techav-homebrew/Wrap030-ATX/Mainboard/Bus-Ctrl.kicad_sch

## KiCad design Mainboard/Bus-Ctrl.kicad_sch (2023-04-03)

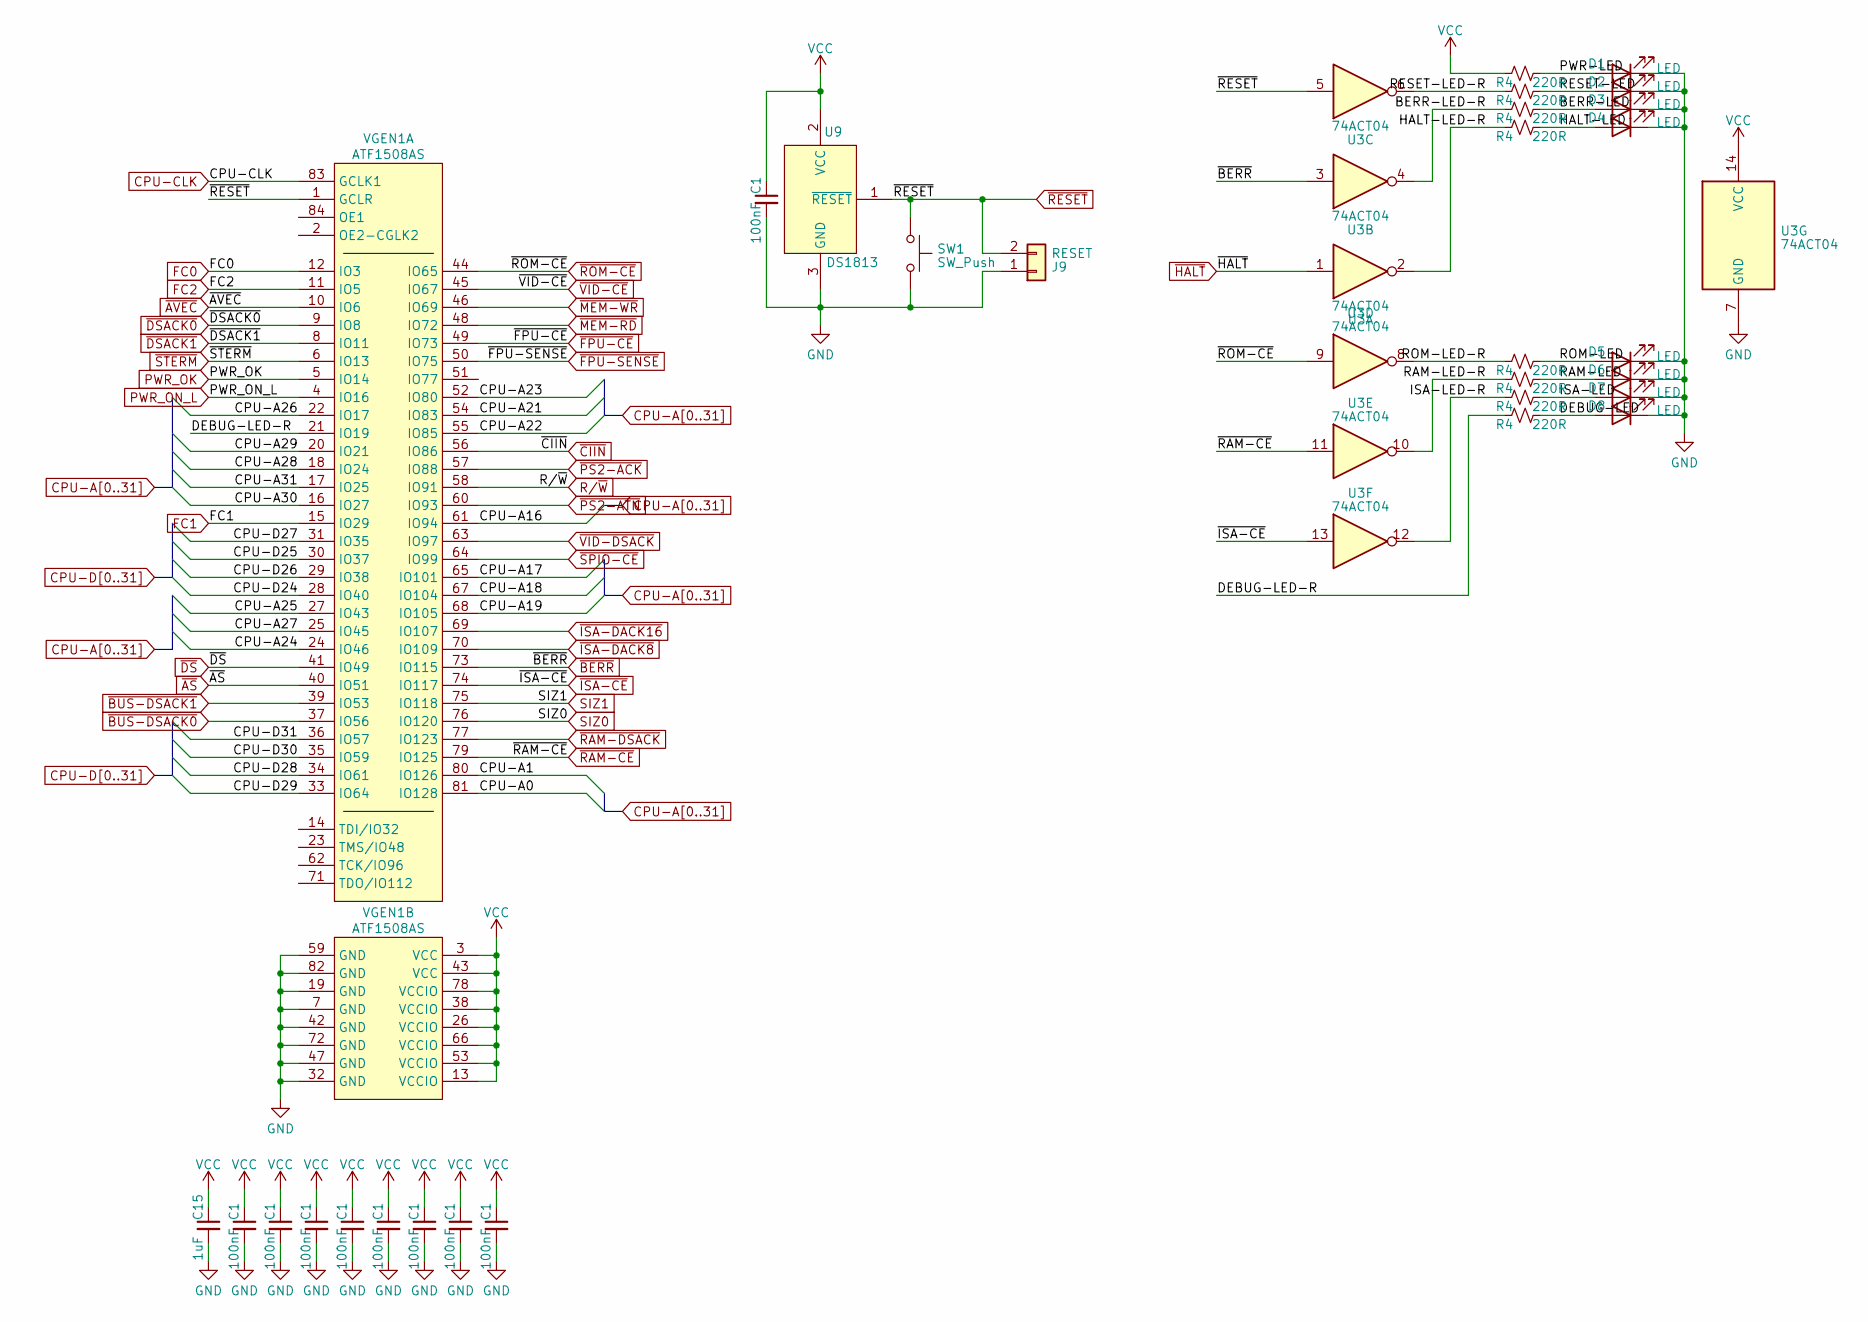
[picture p3: schematic Bus-Ctrl.kicad_sch]

Parts:
C1: 100nF; C_0402_1005Metric_Pad0.74x0.62mm_HandSolder; Mouser-Part 187-CL05B104KO5NNNC
C15: 1uF; C_0402_1005Metric_Pad0.74x0.62mm_HandSolder; Mouser-Part 187-CL05A105KA5NQNC
D1, D2, D3, D4, D5, D6, D7, D8: LED; LED_D3.0mm; Mouser-Part 859-LTL1CHJETNN
J9: RESET; PinHeader_1x02_P2.54mm_Vertical; Mouser-Part 523-G800NA306018EU
R4: 220R; R_0402_1005Metric_Pad0.72x0.64mm_HandSolder; Mouser-Part 303-0402WGF2200TCE
SW1: SW_Push; SW_PUSH_6mm; Mouser-Part 179-TS026660BK260LCR
U3: 74ACT04; DIP-14_W7.62mm_Socket; Mouser-Part 595-SN74ACT04N
U9: DS1813; TO-92_Inline; Mouser-Part 700-DS1813-5T&R
VGEN1: ATF1508AS; PLCC-84_THT-Socket; Mouser-Part 556-ATF1508AS-10JU84

Connections:
BERR-LED: D3.2 (A), R4.2
BERR-LED-R: R4.1, U3.4
CPU-A0: VGEN1.81 (IO128)
CPU-A1: VGEN1.80 (IO126)
CPU-A16: VGEN1.61 (IO94)
CPU-A17: VGEN1.65 (IO101)
CPU-A18: VGEN1.67 (IO104)
CPU-A19: VGEN1.68 (IO105)
CPU-A21: VGEN1.54 (IO83)
CPU-A22: VGEN1.55 (IO85)
CPU-A23: VGEN1.52 (IO80)
CPU-A24: VGEN1.24 (IO46)
CPU-A25: VGEN1.27 (IO43)
CPU-A26: VGEN1.22 (IO17)
CPU-A27: VGEN1.25 (IO45)
CPU-A28: VGEN1.18 (IO24)
CPU-A29: VGEN1.20 (IO21)
CPU-A30: VGEN1.16 (IO27)
CPU-A31: VGEN1.17 (IO25)
CPU-CLK: VGEN1.83 (GCLK1)
CPU-D24: VGEN1.28 (IO40)
CPU-D25: VGEN1.30 (IO37)
CPU-D26: VGEN1.29 (IO38)
CPU-D27: VGEN1.31 (IO35)
CPU-D28: VGEN1.34 (IO61)
CPU-D29: VGEN1.33 (IO64)
CPU-D30: VGEN1.35 (IO59)
CPU-D31: VGEN1.36 (IO57)
DEBUG-LED: D8.2 (A), R4.2
DEBUG-LED-R: R4.1, VGEN1.21 (IO19)
FC0: VGEN1.12 (IO3)
FC1: VGEN1.15 (IO29)
FC2: VGEN1.11 (IO5)
GND: C1.2, C15.2, D1.1 (K), D2.1 (K), D3.1 (K), D4.1 (K), D5.1 (K), D6.1 (K), D7.1 (K), D8.1 (K), J9.1, SW1.2, U3.7 (GND), U9.3 (GND), VGEN1.7 (GND), VGEN1.19 (GND), VGEN1.32 (GND), VGEN1.42 (GND), VGEN1.47 (GND), VGEN1.59 (GND), VGEN1.72 (GND), VGEN1.82 (GND)
HALT-LED: D4.2 (A), R4.2
HALT-LED-R: R4.1, U3.2
ISA-LED: D7.2 (A), R4.2
ISA-LED-R: R4.1, U3.12
PWR-LED: D1.2 (A), R4.2
PWR_OK: VGEN1.5 (IO14)
PWR_ON_L: VGEN1.4 (IO16)
RAM-LED: D6.2 (A), R4.2
RAM-LED-R: R4.1, U3.10
RESET-LED: D2.2 (A), R4.2
RESET-LED-R: R4.1, U3.6
ROM-LED: D5.2 (A), R4.2
ROM-LED-R: R4.1, U3.8
R/~W: VGEN1.58 (IO91)
SIZ0: VGEN1.76 (IO120)
SIZ1: VGEN1.75 (IO118)
VCC: C1.1, C15.1, R4.1, U3.14 (VCC), U9.2 (VCC), VGEN1.3 (VCC), VGEN1.13 (VCCIO), VGEN1.26 (VCCIO), VGEN1.38 (VCCIO), VGEN1.43 (VCC), VGEN1.53 (VCCIO), VGEN1.66 (VCCIO), VGEN1.78 (VCCIO)
~AS: VGEN1.40 (IO51)
~AVEC: VGEN1.10 (IO6)
~BERR: U3.3, VGEN1.73 (IO115)
~BUS-DSACK0: VGEN1.37 (IO56)
~BUS-DSACK1: VGEN1.39 (IO53)
~CIIN: VGEN1.56 (IO86)
~DSACK0: VGEN1.9 (IO8)
~DSACK1: VGEN1.8 (IO11)
~DS: VGEN1.41 (IO49)
~FPU-CE: VGEN1.49 (IO73)
~FPU-SENSE: VGEN1.50 (IO75)
~HALT: U3.1
~ISA-CE: U3.13, VGEN1.74 (IO117)
~ISA-DACK8: VGEN1.70 (IO109)
~ISA-DACK16: VGEN1.69 (IO107)
~MEM-RD: VGEN1.48 (IO72)
~MEM-WR: VGEN1.46 (IO69)
~PS2-ACK: VGEN1.57 (IO88)
~PS2-ATN: VGEN1.60 (IO93)
~RAM-CE: U3.11, VGEN1.79 (IO125)
~RAM-DSACK: VGEN1.77 (IO123)
~RESET: J9.2, SW1.1, U3.5, U9.1 (~RESET), VGEN1.1 (GCLR)
~ROM-CE: U3.9, VGEN1.44 (IO65)
~SPIO-CE: VGEN1.64 (IO99)
~STERM: VGEN1.6 (IO13)
~VID-CE: VGEN1.45 (IO67)
~VID-DSACK: VGEN1.63 (IO97)
