techav-homebrew/Wrap030-ATX/Mainboard/IRQ.kicad_sch

## KiCad design Mainboard/IRQ.kicad_sch (2023-04-03)

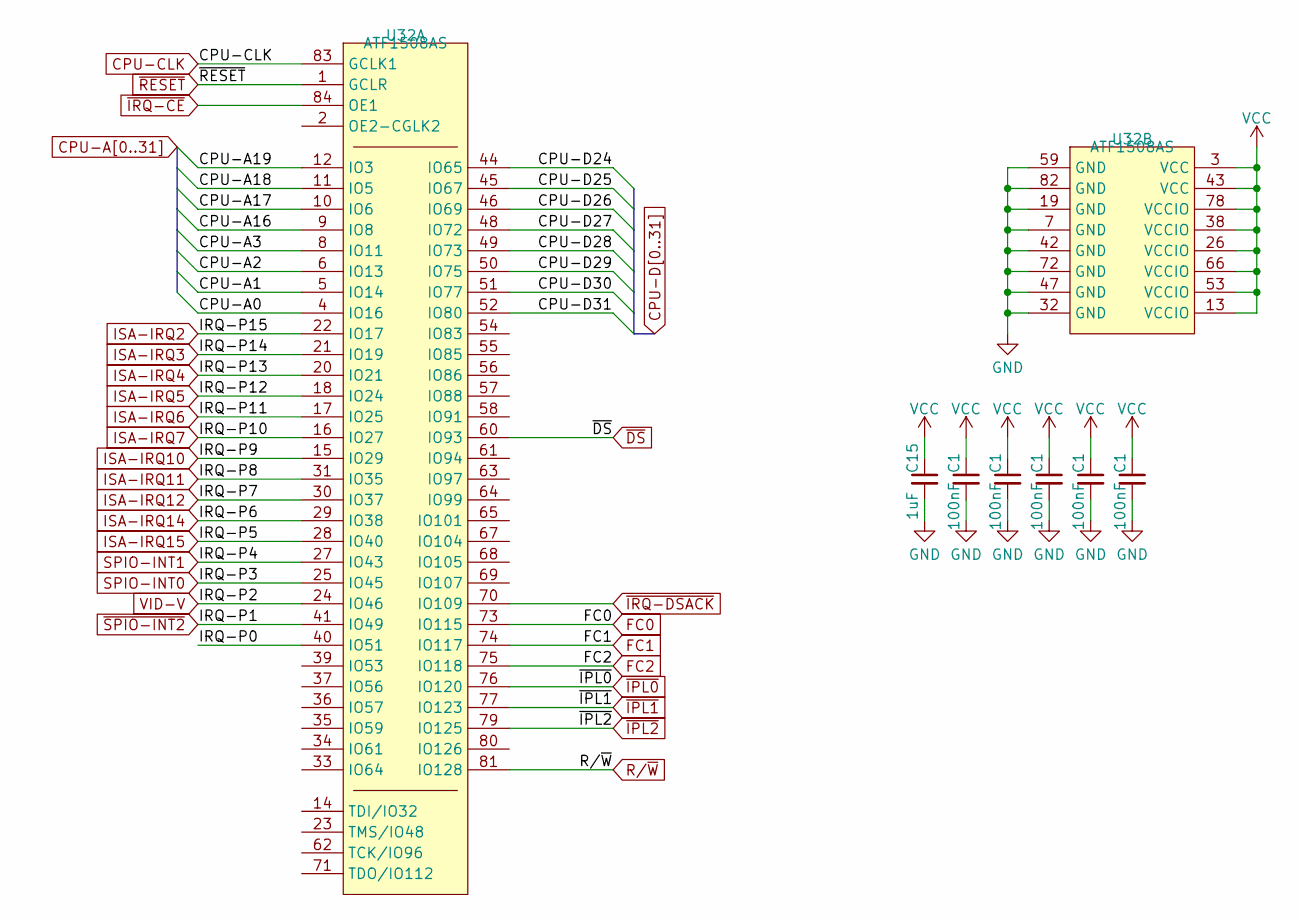
[picture p4: schematic IRQ.kicad_sch]

Parts:
C1: 100nF; C_0402_1005Metric_Pad0.74x0.62mm_HandSolder; Mouser-Part 187-CL05B104KO5NNNC
C15: 1uF; C_0402_1005Metric_Pad0.74x0.62mm_HandSolder; Mouser-Part 187-CL05A105KA5NQNC
U32: ATF1508AS; PLCC-84_THT-Socket; Mouser-Part 556-ATF1508AS-10JU84

Connections:
CPU-A0: U32.4 (IO16)
CPU-A1: U32.5 (IO14)
CPU-A2: U32.6 (IO13)
CPU-A3: U32.8 (IO11)
CPU-A16: U32.9 (IO8)
CPU-A17: U32.10 (IO6)
CPU-A18: U32.11 (IO5)
CPU-A19: U32.12 (IO3)
CPU-CLK: U32.83 (GCLK1)
CPU-D24: U32.44 (IO65)
CPU-D25: U32.45 (IO67)
CPU-D26: U32.46 (IO69)
CPU-D27: U32.48 (IO72)
CPU-D28: U32.49 (IO73)
CPU-D29: U32.50 (IO75)
CPU-D30: U32.51 (IO77)
CPU-D31: U32.52 (IO80)
FC0: U32.73 (IO115)
FC1: U32.74 (IO117)
FC2: U32.75 (IO118)
GND: C1.2, C15.2, U32.7 (GND), U32.19 (GND), U32.32 (GND), U32.42 (GND), U32.47 (GND), U32.59 (GND), U32.72 (GND), U32.82 (GND)
IRQ-P0: U32.40 (IO51)
ISA-IRQ2: U32.22 (IO17)
ISA-IRQ3: U32.21 (IO19)
ISA-IRQ4: U32.20 (IO21)
ISA-IRQ5: U32.18 (IO24)
ISA-IRQ6: U32.17 (IO25)
ISA-IRQ7: U32.16 (IO27)
ISA-IRQ10: U32.15 (IO29)
ISA-IRQ11: U32.31 (IO35)
ISA-IRQ12: U32.30 (IO37)
ISA-IRQ14: U32.29 (IO38)
ISA-IRQ15: U32.28 (IO40)
R/~W: U32.81 (IO128)
SPIO-INT0: U32.25 (IO45)
SPIO-INT1: U32.27 (IO43)
VCC: C1.1, C15.1, U32.3 (VCC), U32.13 (VCCIO), U32.26 (VCCIO), U32.38 (VCCIO), U32.43 (VCC), U32.53 (VCCIO), U32.66 (VCCIO), U32.78 (VCCIO)
VID-V: U32.24 (IO46)
~DS: U32.60 (IO93)
~IPL0: U32.76 (IO120)
~IPL1: U32.77 (IO123)
~IPL2: U32.79 (IO125)
~IRQ-CE: U32.84 (OE1)
~IRQ-DSACK: U32.70 (IO109)
~RESET: U32.1 (GCLR)
~SPIO-INT2: U32.41 (IO49)
