techav-homebrew/Wrap030-ATX/Mainboard/ISA-IDE-Con.kicad_sch

## KiCad design Mainboard/ISA-IDE-Con.kicad_sch (2023-04-03)

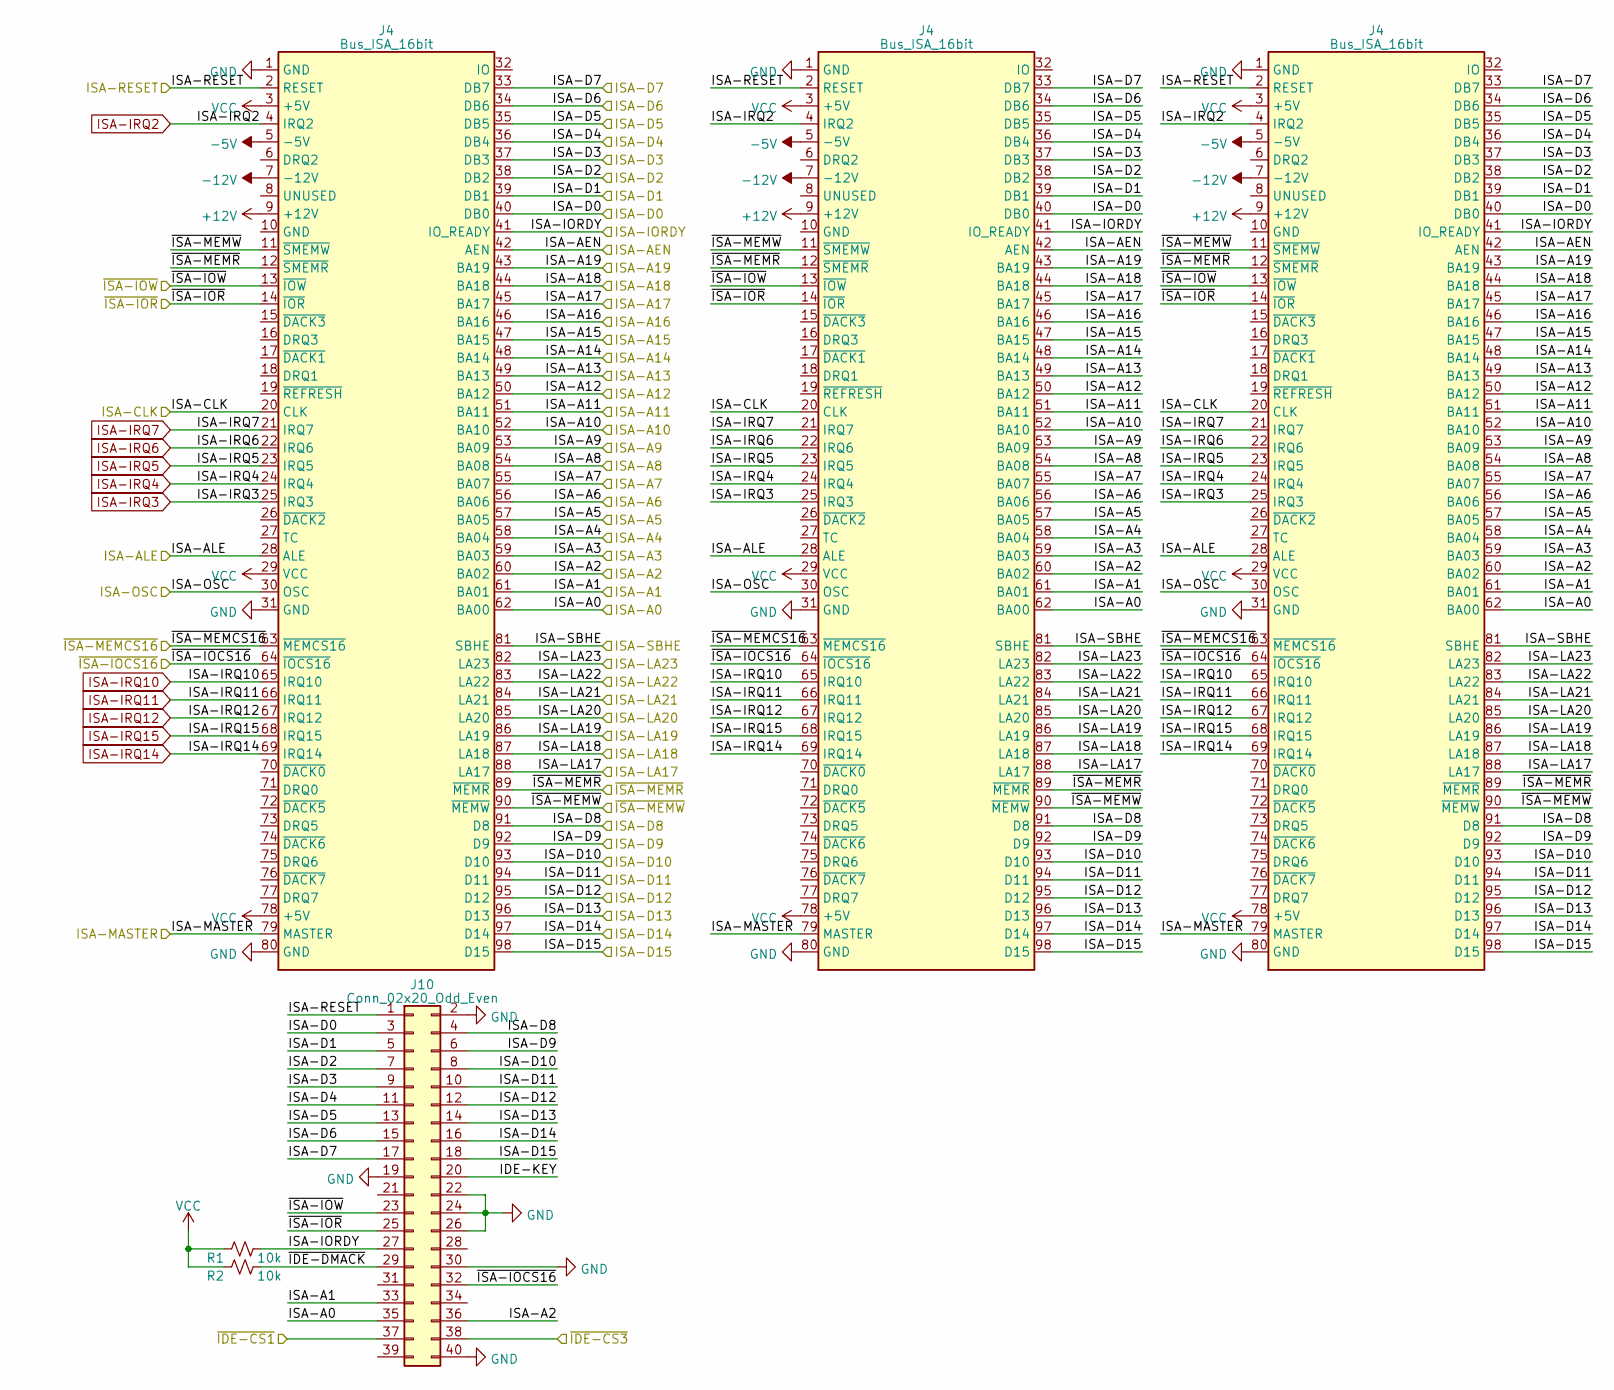
[picture p5: schematic ISA-IDE-Con.kicad_sch]

Parts:
J4: Bus_ISA_16bit; ISA16; Mouser-Part 571-5645169-4
J10: Conn_02x20_Odd_Even; PinHeader_2x20_P2.54mm_Vertical; Mouser-Part 710-61203921621
R1, R2: 10k; R_0402_1005Metric_Pad0.72x0.64mm_HandSolder; Mouser-Part 303-0402WGF1002TCE

Connections:
+12V: J4.9 (+12V)
-5V: J4.5 (-5V)
-12V: J4.7 (-12V)
GND: J4.1 (GND), J4.31 (GND), J4.80 (GND), J10.2, J10.19, J10.22, J10.24, J10.26, J10.30, J10.40
IDE-KEY: J10.20
ISA-A0: J4.62 (BA00), J10.35
ISA-A1: J4.61 (BA01), J10.33
ISA-A2: J4.60 (BA02), J10.36
ISA-A3: J4.59 (BA03)
ISA-A4: J4.58 (BA04)
ISA-A5: J4.57 (BA05)
ISA-A6: J4.56 (BA06)
ISA-A7: J4.55 (BA07)
ISA-A8: J4.54 (BA08)
ISA-A9: J4.53 (BA09)
ISA-A10: J4.52 (BA10)
ISA-A11: J4.51 (BA11)
ISA-A12: J4.50 (BA12)
ISA-A13: J4.49 (BA13)
ISA-A14: J4.48 (BA14)
ISA-A15: J4.47 (BA15)
ISA-A16: J4.46 (BA16)
ISA-A17: J4.45 (BA17)
ISA-A18: J4.44 (BA18)
ISA-A19: J4.43 (BA19)
ISA-AEN: J4.42 (AEN)
ISA-ALE: J4.28 (ALE)
ISA-CLK: J4.20 (CLK)
ISA-D0: J4.40 (DB0), J10.3
ISA-D1: J4.39 (DB1), J10.5
ISA-D2: J4.38 (DB2), J10.7
ISA-D3: J4.37 (DB3), J10.9
ISA-D4: J4.36 (DB4), J10.11
ISA-D5: J4.35 (DB5), J10.13
ISA-D6: J4.34 (DB6), J10.15
ISA-D7: J4.33 (DB7), J10.17
ISA-D8: J4.91 (D8), J10.4
ISA-D9: J4.92 (D9), J10.6
ISA-D10: J4.93 (D10), J10.8
ISA-D11: J4.94 (D11), J10.10
ISA-D12: J4.95 (D12), J10.12
ISA-D13: J4.96 (D13), J10.14
ISA-D14: J4.97 (D14), J10.16
ISA-D15: J4.98 (D15), J10.18
ISA-IORDY: J4.41 (IO_READY), J10.27, R1.2
ISA-IRQ2: J4.4 (IRQ2)
ISA-IRQ3: J4.25 (IRQ3)
ISA-IRQ4: J4.24 (IRQ4)
ISA-IRQ5: J4.23 (IRQ5)
ISA-IRQ6: J4.22 (IRQ6)
ISA-IRQ7: J4.21 (IRQ7)
ISA-IRQ10: J4.65 (IRQ10)
ISA-IRQ11: J4.66 (IRQ11)
ISA-IRQ12: J4.67 (IRQ12)
ISA-IRQ14: J4.69 (IRQ14)
ISA-IRQ15: J4.68 (IRQ15)
ISA-LA17: J4.88 (LA17)
ISA-LA18: J4.87 (LA18)
ISA-LA19: J4.86 (LA19)
ISA-LA20: J4.85 (LA20)
ISA-LA21: J4.84 (LA21)
ISA-LA22: J4.83 (LA22)
ISA-LA23: J4.82 (LA23)
ISA-MASTER: J4.79 (MASTER)
ISA-OSC: J4.30 (OSC)
ISA-RESET: J4.2 (RESET), J10.1
ISA-SBHE: J4.81 (SBHE)
VCC: J4.3 (+5V), J4.29 (VCC), J4.78 (+5V), R1.1, R2.1
~IDE-CS1: J10.37
~IDE-CS3: J10.38
~IDE-DMACK: J10.29, R2.2
~ISA-IOCS16: J4.64 (~IOCS16), J10.32
~ISA-IOR: J4.14 (~IOR), J10.25
~ISA-IOW: J4.13 (~IOW), J10.23
~ISA-MEMCS16: J4.63 (~MEMCS16)
~ISA-MEMR: J4.12 (~SMEMR), J4.89 (~MEMR)
~ISA-MEMW: J4.11 (~SMEMW), J4.90 (~MEMW)
