techav-homebrew/Wrap030-ATX/Mainboard/ISA-IDE.kicad_sch

## KiCad design Mainboard/ISA-IDE.kicad_sch (2023-04-03)

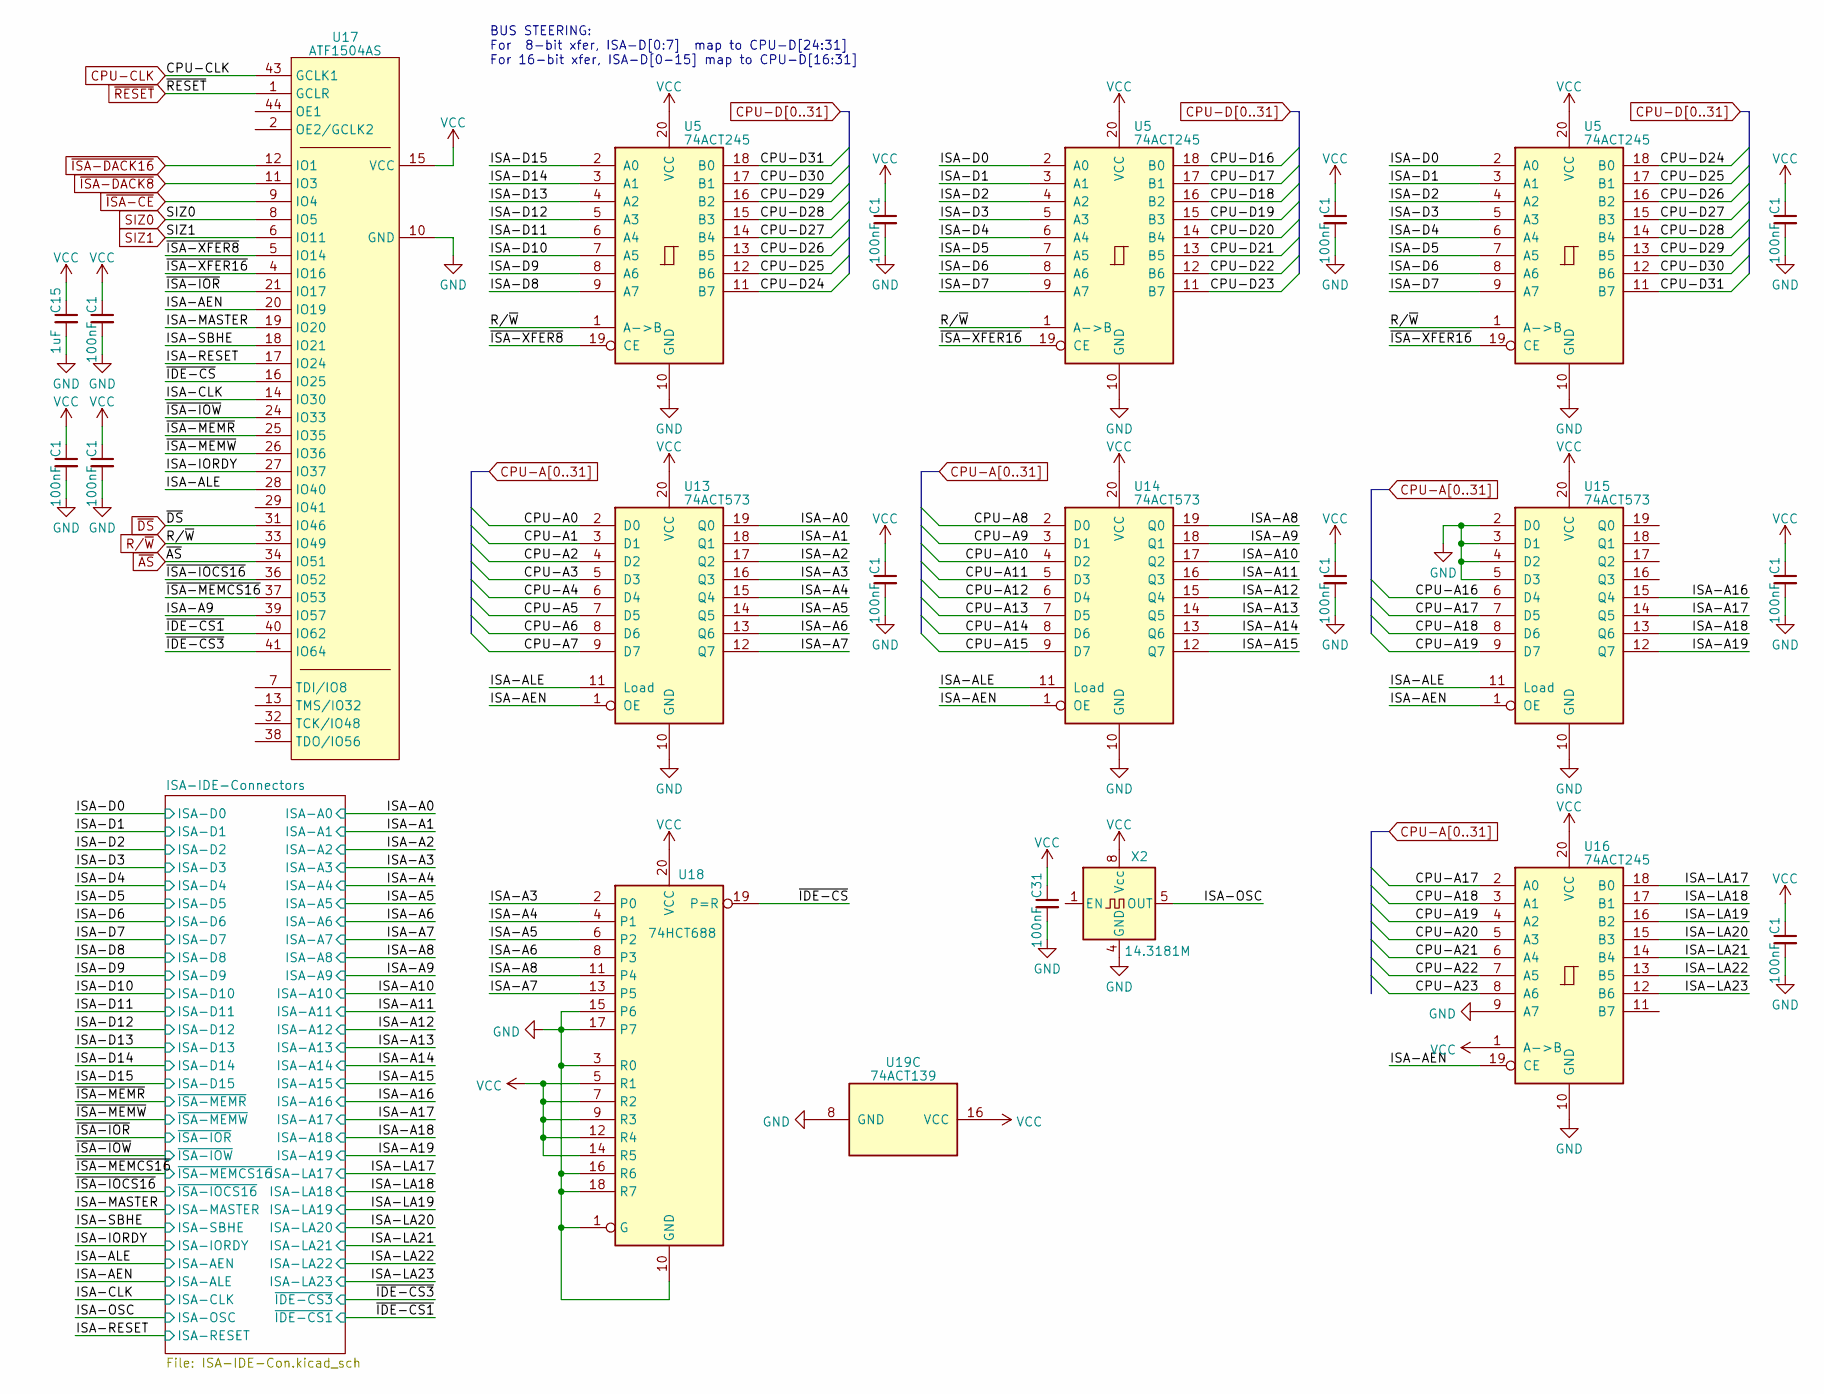
[picture p6: schematic ISA-IDE.kicad_sch]

Parts:
C1, C31: 100nF; C_0402_1005Metric_Pad0.74x0.62mm_HandSolder; Mouser-Part 187-CL05B104KO5NNNC
C15: 1uF; C_0402_1005Metric_Pad0.74x0.62mm_HandSolder; Mouser-Part 187-CL05A105KA5NQNC
U5, U16: 74ACT245; DIP-20_W7.62mm_Socket; Mouser-Part 595-SN74ACT245N
U13, U14, U15: 74ACT573; DIP-20_W7.62mm_Socket; Mouser-Part 595-SN74ACT573N
U17: ATF1504AS; PLCC-44_THT-Socket; Mouser-Part 556-AF1500A10JU
U18: 74HCT688; DIP-20_W7.62mm_Socket; Mouser-Part 595-CD74HCT688EE4
U19: 74ACT139; DIP-16_W7.62mm_Socket; Mouser-Part 595-CD74ACT139E
X2: 14.3181M; Oscillator_DIP-8; Mouser-Part ECS-2100AX-14.31818MHZ

Connections:
CPU-A0: U13.2 (D0)
CPU-A1: U13.3 (D1)
CPU-A2: U13.4 (D2)
CPU-A3: U13.5 (D3)
CPU-A4: U13.6 (D4)
CPU-A5: U13.7 (D5)
CPU-A6: U13.8 (D6)
CPU-A7: U13.9 (D7)
CPU-A8: U14.2 (D0)
CPU-A9: U14.3 (D1)
CPU-A10: U14.4 (D2)
CPU-A11: U14.5 (D3)
CPU-A12: U14.6 (D4)
CPU-A13: U14.7 (D5)
CPU-A14: U14.8 (D6)
CPU-A15: U14.9 (D7)
CPU-A16: U15.6 (D4)
CPU-A17: U15.7 (D5), U16.2 (A0)
CPU-A18: U15.8 (D6), U16.3 (A1)
CPU-A19: U15.9 (D7), U16.4 (A2)
CPU-A20: U16.5 (A3)
CPU-A21: U16.6 (A4)
CPU-A22: U16.7 (A5)
CPU-A23: U16.8 (A6)
CPU-CLK: U17.43 (GCLK1)
CPU-D16: U5.18 (B0)
CPU-D17: U5.17 (B1)
CPU-D18: U5.16 (B2)
CPU-D19: U5.15 (B3)
CPU-D20: U5.14 (B4)
CPU-D21: U5.13 (B5)
CPU-D22: U5.12 (B6)
CPU-D23: U5.11 (B7)
CPU-D24: U5.11 (B7), U5.18 (B0)
CPU-D25: U5.12 (B6), U5.17 (B1)
CPU-D26: U5.13 (B5), U5.16 (B2)
CPU-D27: U5.14 (B4), U5.15 (B3)
CPU-D28: U5.14 (B4), U5.15 (B3)
CPU-D29: U5.13 (B5), U5.16 (B2)
CPU-D30: U5.12 (B6), U5.17 (B1)
CPU-D31: U5.11 (B7), U5.18 (B0)
GND: C1.2, C15.2, C31.2, U5.10 (GND), U13.10 (GND), U14.10 (GND), U15.2 (D0), U15.3 (D1), U15.4 (D2), U15.5 (D3), U15.10 (GND), U16.9 (A7), U16.10 (GND), U17.10 (GND), U17.22 (GND), U17.30 (GND), U17.42 (GND), U18.1 (G), U18.3 (R0), U18.10 (GND), U18.15 (P6), U18.16 (R6), U18.17 (P7), U18.18 (R7), U19.8 (GND), X2.4 (GND)
ISA-A0: U13.19 (Q0)
ISA-A1: U13.18 (Q1)
ISA-A2: U13.17 (Q2)
ISA-A3: U13.16 (Q3), U18.2 (P0)
ISA-A4: U13.15 (Q4), U18.4 (P1)
ISA-A5: U13.14 (Q5), U18.6 (P2)
ISA-A6: U13.13 (Q6), U18.8 (P3)
ISA-A7: U13.12 (Q7), U18.13 (P5)
ISA-A8: U14.19 (Q0), U18.11 (P4)
ISA-A9: U14.18 (Q1), U17.39 (IO57)
ISA-A10: U14.17 (Q2)
ISA-A11: U14.16 (Q3)
ISA-A12: U14.15 (Q4)
ISA-A13: U14.14 (Q5)
ISA-A14: U14.13 (Q6)
ISA-A15: U14.12 (Q7)
ISA-A16: U15.15 (Q4)
ISA-A17: U15.14 (Q5)
ISA-A18: U15.13 (Q6)
ISA-A19: U15.12 (Q7)
ISA-AEN: U13.1 (OE), U14.1 (OE), U15.1 (OE), U16.19 (CE), U17.20 (IO19)
ISA-ALE: U13.11 (Load), U14.11 (Load), U15.11 (Load), U17.28 (IO40)
ISA-CLK: U17.14 (IO30)
ISA-D0: U5.2 (A0)
ISA-D1: U5.3 (A1)
ISA-D2: U5.4 (A2)
ISA-D3: U5.5 (A3)
ISA-D4: U5.6 (A4)
ISA-D5: U5.7 (A5)
ISA-D6: U5.8 (A6)
ISA-D7: U5.9 (A7)
ISA-D8: U5.9 (A7)
ISA-D9: U5.8 (A6)
ISA-D10: U5.7 (A5)
ISA-D11: U5.6 (A4)
ISA-D12: U5.5 (A3)
ISA-D13: U5.4 (A2)
ISA-D14: U5.3 (A1)
ISA-D15: U5.2 (A0)
ISA-IORDY: U17.27 (IO37)
ISA-LA17: U16.18 (B0)
ISA-LA18: U16.17 (B1)
ISA-LA19: U16.16 (B2)
ISA-LA20: U16.15 (B3)
ISA-LA21: U16.14 (B4)
ISA-LA22: U16.13 (B5)
ISA-LA23: U16.12 (B6)
ISA-MASTER: U17.19 (IO20)
ISA-OSC: X2.5 (OUT)
ISA-RESET: U17.17 (IO24)
ISA-SBHE: U17.18 (IO21)
R/~W: U5.1 (A->B), U17.33 (IO49)
SIZ0: U17.8 (IO5)
SIZ1: U17.6 (IO11)
VCC: C1.1, C15.1, C31.1, U5.20 (VCC), U13.20 (VCC), U14.20 (VCC), U15.20 (VCC), U16.1 (A->B), U16.20 (VCC), U17.15 (VCC), U17.23 (VCC), U17.35 (VCC), U18.5 (R1), U18.7 (R2), U18.9 (R3), U18.12 (R4), U18.14 (R5), U18.20 (VCC), U19.16 (VCC), X2.8 (Vcc)
~AS: U17.34 (IO51)
~DS: U17.31 (IO46)
~IDE-CS1: U17.40 (IO62)
~IDE-CS3: U17.41 (IO64)
~IDE-CS: U17.16 (IO25), U18.19 (P=R)
~ISA-CE: U17.9 (IO4)
~ISA-DACK8: U17.11 (IO3)
~ISA-DACK16: U17.12 (IO1)
~ISA-IOCS16: U17.36 (IO52)
~ISA-IOR: U17.21 (IO17)
~ISA-IOW: U17.24 (IO33)
~ISA-MEMCS16: U17.37 (IO53)
~ISA-MEMR: U17.25 (IO35)
~ISA-MEMW: U17.26 (IO36)
~ISA-XFER8: U5.19 (CE), U17.5 (IO14)
~ISA-XFER16: U5.19 (CE), U17.4 (IO16)
~RESET: U17.1 (GCLR)

Notes on the sheet:
BUS STEERING: For 8-bit xfer, ISA-D[0:7] map to CPU-D[24:31] For 16-bit xfer, ISA-D[0-15] map to CPU-D[16:31]
