techav-homebrew/Wrap030-ATX/Mainboard/MainMem.kicad_sch

## KiCad design Mainboard/MainMem.kicad_sch (2023-04-03)

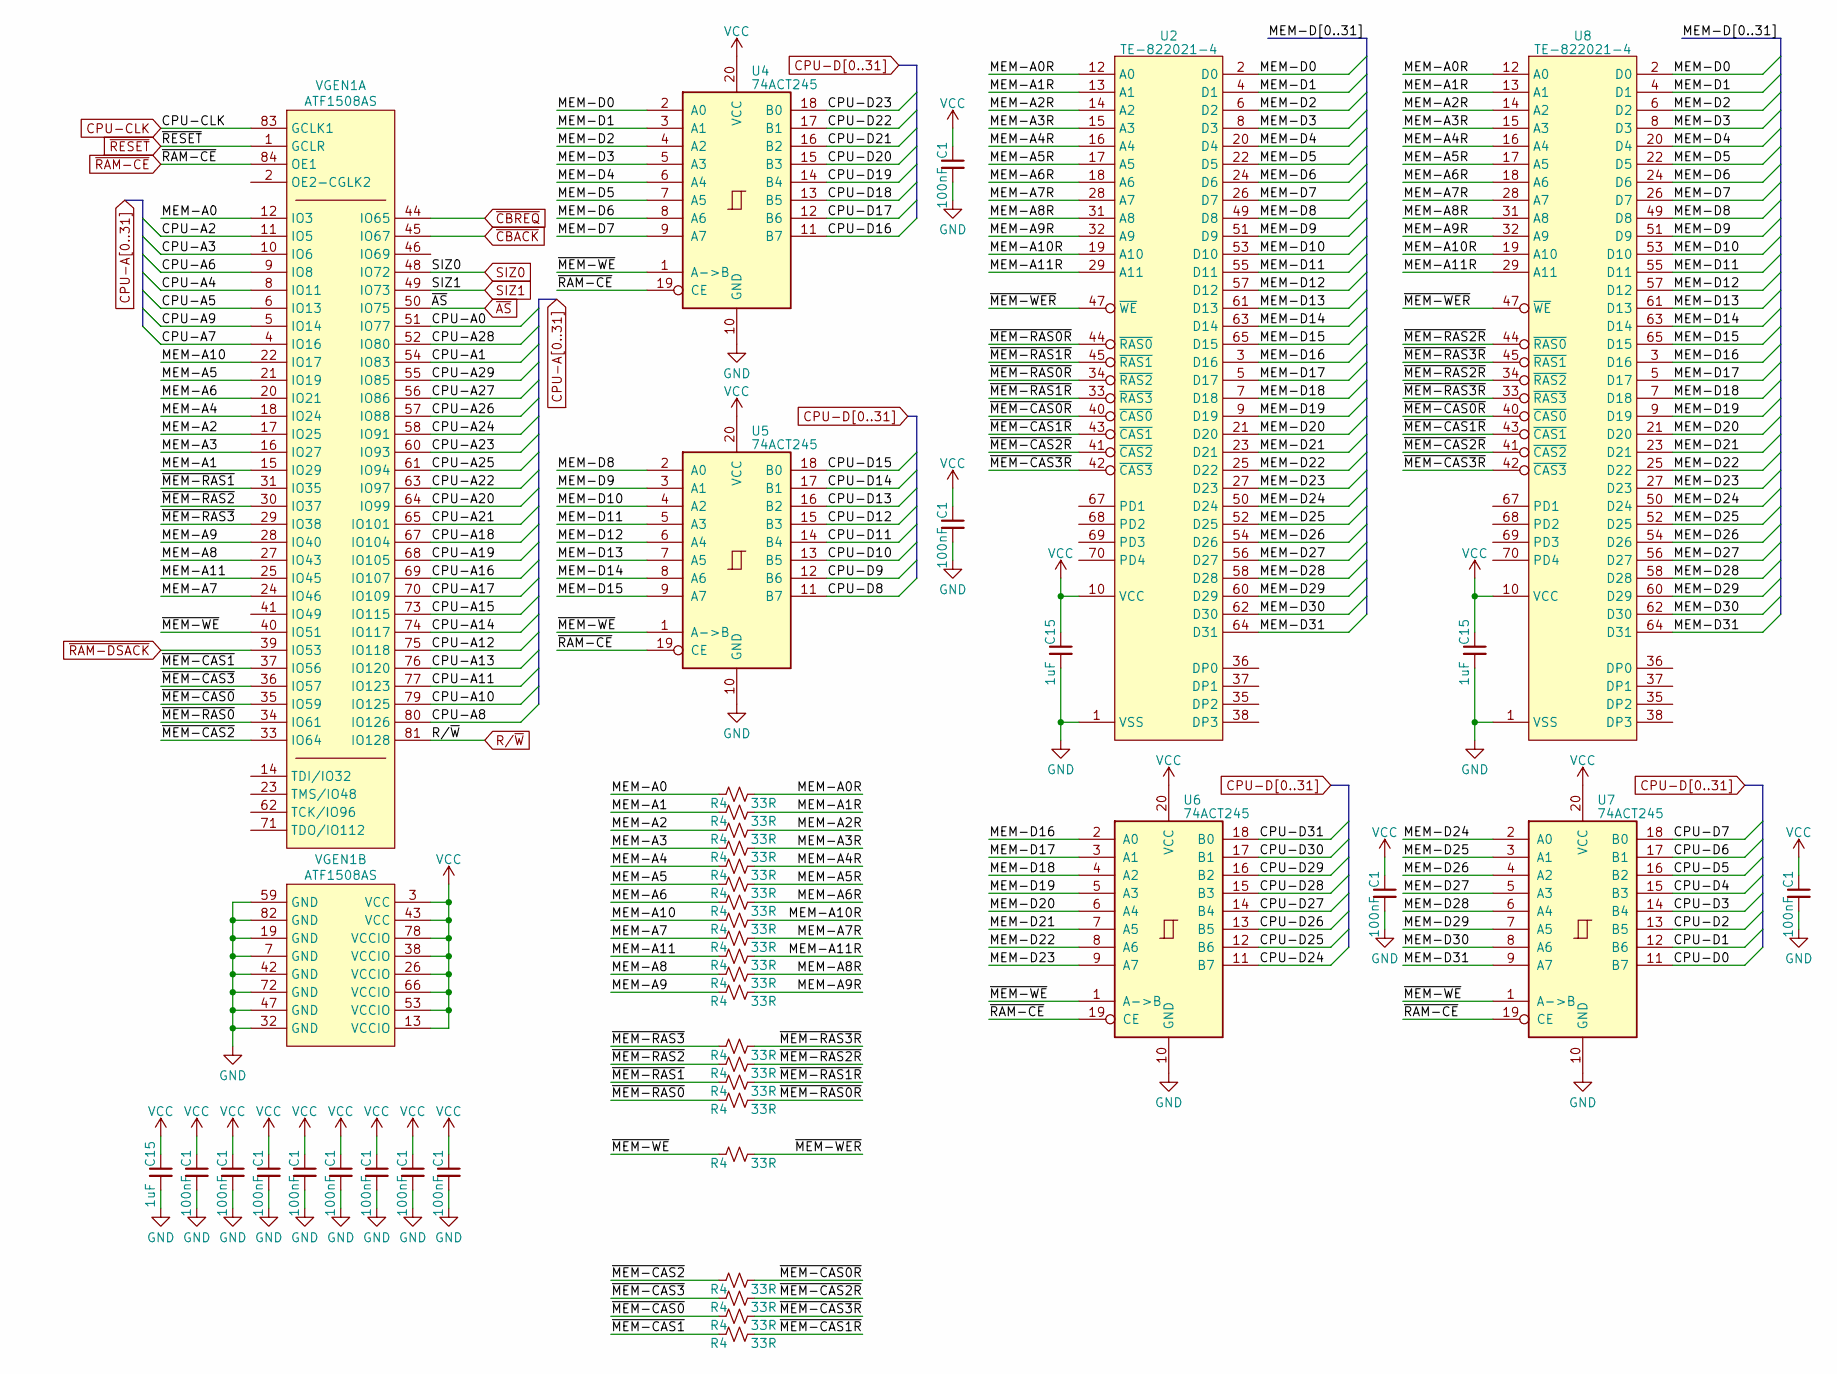
[picture p7: schematic MainMem.kicad_sch]

Parts:
C1: 100nF; C_0402_1005Metric_Pad0.74x0.62mm_HandSolder; Mouser-Part 187-CL05B104KO5NNNC
C15: 1uF; C_0402_1005Metric_Pad0.74x0.62mm_HandSolder; Mouser-Part 187-CL05A105KA5NQNC
R4: 33R; R_0603_1608Metric_Pad0.98x0.95mm_HandSolder; Mouser-Part 303-0603WAF330JT5E
U2, U8: TE-822021-4; SIMM72; Mouser-Part 571-5822021-4
U4, U5, U6, U7: 74ACT245; DIP-20_W7.62mm_Socket; Mouser-Part 595-SN74ACT245N
VGEN1: ATF1508AS; PLCC-84_THT-Socket; Mouser-Part 556-ATF1508AS-10JU84

Connections:
CPU-A0: VGEN1.51 (IO77)
CPU-A1: VGEN1.54 (IO83)
CPU-A2: VGEN1.11 (IO5)
CPU-A3: VGEN1.10 (IO6)
CPU-A4: VGEN1.8 (IO11)
CPU-A5: VGEN1.6 (IO13)
CPU-A6: VGEN1.9 (IO8)
CPU-A7: VGEN1.4 (IO16)
CPU-A8: VGEN1.80 (IO126)
CPU-A9: VGEN1.5 (IO14)
CPU-A10: VGEN1.79 (IO125)
CPU-A11: VGEN1.77 (IO123)
CPU-A12: VGEN1.75 (IO118)
CPU-A13: VGEN1.76 (IO120)
CPU-A14: VGEN1.74 (IO117)
CPU-A15: VGEN1.73 (IO115)
CPU-A16: VGEN1.69 (IO107)
CPU-A17: VGEN1.70 (IO109)
CPU-A18: VGEN1.67 (IO104)
CPU-A19: VGEN1.68 (IO105)
CPU-A20: VGEN1.64 (IO99)
CPU-A21: VGEN1.65 (IO101)
CPU-A22: VGEN1.63 (IO97)
CPU-A23: VGEN1.60 (IO93)
CPU-A24: VGEN1.58 (IO91)
CPU-A25: VGEN1.61 (IO94)
CPU-A26: VGEN1.57 (IO88)
CPU-A27: VGEN1.56 (IO86)
CPU-A28: VGEN1.52 (IO80)
CPU-A29: VGEN1.55 (IO85)
CPU-CLK: VGEN1.83 (GCLK1)
CPU-D0: U7.11 (B7)
CPU-D1: U7.12 (B6)
CPU-D2: U7.13 (B5)
CPU-D3: U7.14 (B4)
CPU-D4: U7.15 (B3)
CPU-D5: U7.16 (B2)
CPU-D6: U7.17 (B1)
CPU-D7: U7.18 (B0)
CPU-D8: U5.11 (B7)
CPU-D9: U5.12 (B6)
CPU-D10: U5.13 (B5)
CPU-D11: U5.14 (B4)
CPU-D12: U5.15 (B3)
CPU-D13: U5.16 (B2)
CPU-D14: U5.17 (B1)
CPU-D15: U5.18 (B0)
CPU-D16: U4.11 (B7)
CPU-D17: U4.12 (B6)
CPU-D18: U4.13 (B5)
CPU-D19: U4.14 (B4)
CPU-D20: U4.15 (B3)
CPU-D21: U4.16 (B2)
CPU-D22: U4.17 (B1)
CPU-D23: U4.18 (B0)
CPU-D24: U6.11 (B7)
CPU-D25: U6.12 (B6)
CPU-D26: U6.13 (B5)
CPU-D27: U6.14 (B4)
CPU-D28: U6.15 (B3)
CPU-D29: U6.16 (B2)
CPU-D30: U6.17 (B1)
CPU-D31: U6.18 (B0)
GND: C1.2, C15.2, U2.1 (VSS), U2.39 (VSS), U2.72 (VSS), U4.10 (GND), U5.10 (GND), U6.10 (GND), U7.10 (GND), U8.1 (VSS), U8.39 (VSS), U8.72 (VSS), VGEN1.7 (GND), VGEN1.19 (GND), VGEN1.32 (GND), VGEN1.42 (GND), VGEN1.47 (GND), VGEN1.59 (GND), VGEN1.72 (GND), VGEN1.82 (GND)
MEM-A0: R4.1, VGEN1.12 (IO3)
MEM-A0R: R4.2, U2.12 (A0), U8.12 (A0)
MEM-A1: R4.1, VGEN1.15 (IO29)
MEM-A1R: R4.2, U2.13 (A1), U8.13 (A1)
MEM-A2: R4.1, VGEN1.17 (IO25)
MEM-A2R: R4.2, U2.14 (A2), U8.14 (A2)
MEM-A3: R4.1, VGEN1.16 (IO27)
MEM-A3R: R4.2, U2.15 (A3), U8.15 (A3)
MEM-A4: R4.1, VGEN1.18 (IO24)
MEM-A4R: R4.2, U2.16 (A4), U8.16 (A4)
MEM-A5: R4.1, VGEN1.21 (IO19)
MEM-A5R: R4.2, U2.17 (A5), U8.17 (A5)
MEM-A6: R4.1, VGEN1.20 (IO21)
MEM-A6R: R4.2, U2.18 (A6), U8.18 (A6)
MEM-A7: R4.1, VGEN1.24 (IO46)
MEM-A7R: R4.2, U2.28 (A7), U8.28 (A7)
MEM-A8: R4.1, VGEN1.27 (IO43)
MEM-A8R: R4.2, U2.31 (A8), U8.31 (A8)
MEM-A9: R4.1, VGEN1.28 (IO40)
MEM-A9R: R4.2, U2.32 (A9), U8.32 (A9)
MEM-A10: R4.1, VGEN1.22 (IO17)
MEM-A10R: R4.2, U2.19 (A10), U8.19 (A10)
MEM-A11: R4.1, VGEN1.25 (IO45)
MEM-A11R: R4.2, U2.29 (A11), U8.29 (A11)
MEM-D0: U2.2 (D0), U4.2 (A0), U8.2 (D0)
MEM-D1: U2.4 (D1), U4.3 (A1), U8.4 (D1)
MEM-D2: U2.6 (D2), U4.4 (A2), U8.6 (D2)
MEM-D3: U2.8 (D3), U4.5 (A3), U8.8 (D3)
MEM-D4: U2.20 (D4), U4.6 (A4), U8.20 (D4)
MEM-D5: U2.22 (D5), U4.7 (A5), U8.22 (D5)
MEM-D6: U2.24 (D6), U4.8 (A6), U8.24 (D6)
MEM-D7: U2.26 (D7), U4.9 (A7), U8.26 (D7)
MEM-D8: U2.49 (D8), U5.2 (A0), U8.49 (D8)
MEM-D9: U2.51 (D9), U5.3 (A1), U8.51 (D9)
MEM-D10: U2.53 (D10), U5.4 (A2), U8.53 (D10)
MEM-D11: U2.55 (D11), U5.5 (A3), U8.55 (D11)
MEM-D12: U2.57 (D12), U5.6 (A4), U8.57 (D12)
MEM-D13: U2.61 (D13), U5.7 (A5), U8.61 (D13)
MEM-D14: U2.63 (D14), U5.8 (A6), U8.63 (D14)
MEM-D15: U2.65 (D15), U5.9 (A7), U8.65 (D15)
MEM-D16: U2.3 (D16), U6.2 (A0), U8.3 (D16)
MEM-D17: U2.5 (D17), U6.3 (A1), U8.5 (D17)
MEM-D18: U2.7 (D18), U6.4 (A2), U8.7 (D18)
MEM-D19: U2.9 (D19), U6.5 (A3), U8.9 (D19)
MEM-D20: U2.21 (D20), U6.6 (A4), U8.21 (D20)
MEM-D21: U2.23 (D21), U6.7 (A5), U8.23 (D21)
MEM-D22: U2.25 (D22), U6.8 (A6), U8.25 (D22)
MEM-D23: U2.27 (D23), U6.9 (A7), U8.27 (D23)
MEM-D24: U2.50 (D24), U7.2 (A0), U8.50 (D24)
MEM-D25: U2.52 (D25), U7.3 (A1), U8.52 (D25)
MEM-D26: U2.54 (D26), U7.4 (A2), U8.54 (D26)
MEM-D27: U2.56 (D27), U7.5 (A3), U8.56 (D27)
MEM-D28: U2.58 (D28), U7.6 (A4), U8.58 (D28)
MEM-D29: U2.60 (D29), U7.7 (A5), U8.60 (D29)
MEM-D30: U2.62 (D30), U7.8 (A6), U8.62 (D30)
MEM-D31: U2.64 (D31), U7.9 (A7), U8.64 (D31)
unnamed: U2.11 (NC), U2.46 (NC), U2.48 (NC), U2.66 (NC), U2.71 (NC)
unnamed: U8.11 (NC), U8.46 (NC), U8.48 (NC), U8.66 (NC), U8.71 (NC)
R/~W: VGEN1.81 (IO128)
SIZ0: VGEN1.48 (IO72)
SIZ1: VGEN1.49 (IO73)
VCC: C1.1, C15.1, U2.10 (VCC), U2.30 (VCC), U2.59 (VCC), U4.20 (VCC), U5.20 (VCC), U6.20 (VCC), U7.20 (VCC), U8.10 (VCC), U8.30 (VCC), U8.59 (VCC), VGEN1.3 (VCC), VGEN1.13 (VCCIO), VGEN1.26 (VCCIO), VGEN1.38 (VCCIO), VGEN1.43 (VCC), VGEN1.53 (VCCIO), VGEN1.66 (VCCIO), VGEN1.78 (VCCIO)
~AS: VGEN1.50 (IO75)
~CBACK: VGEN1.45 (IO67)
~CBREQ: VGEN1.44 (IO65)
~MEM-CAS0R: R4.2, U2.40 (~CAS0), U8.40 (~CAS0)
~MEM-CAS0: R4.1, VGEN1.35 (IO59)
~MEM-CAS1R: R4.2, U2.43 (~CAS1), U8.43 (~CAS1)
~MEM-CAS1: R4.1, VGEN1.37 (IO56)
~MEM-CAS2R: R4.2, U2.41 (~CAS2), U8.41 (~CAS2)
~MEM-CAS2: R4.1, VGEN1.33 (IO64)
~MEM-CAS3R: R4.2, U2.42 (~CAS3), U8.42 (~CAS3)
~MEM-CAS3: R4.1, VGEN1.36 (IO57)
~MEM-RAS0R: R4.2, U2.34 (~RAS2), U2.44 (~RAS0)
~MEM-RAS0: R4.1, VGEN1.34 (IO61)
~MEM-RAS1R: R4.2, U2.33 (~RAS3), U2.45 (~RAS1)
~MEM-RAS1: R4.1, VGEN1.31 (IO35)
~MEM-RAS2R: R4.2, U8.34 (~RAS2), U8.44 (~RAS0)
~MEM-RAS2: R4.1, VGEN1.30 (IO37)
~MEM-RAS3R: R4.2, U8.33 (~RAS3), U8.45 (~RAS1)
~MEM-RAS3: R4.1, VGEN1.29 (IO38)
~MEM-WER: R4.2, U2.47 (~WE), U8.47 (~WE)
~MEM-WE: R4.1, U4.1 (A->B), U5.1 (A->B), U6.1 (A->B), U7.1 (A->B), VGEN1.40 (IO51)
~RAM-CE: U4.19 (CE), U5.19 (CE), U6.19 (CE), U7.19 (CE), VGEN1.84 (OE1)
~RAM-DSACK: VGEN1.39 (IO53)
~RESET: VGEN1.1 (GCLR)
