techav-homebrew/Wrap030-ATX/Mainboard/ROM.kicad_sch

## KiCad design Mainboard/ROM.kicad_sch (2023-04-03)

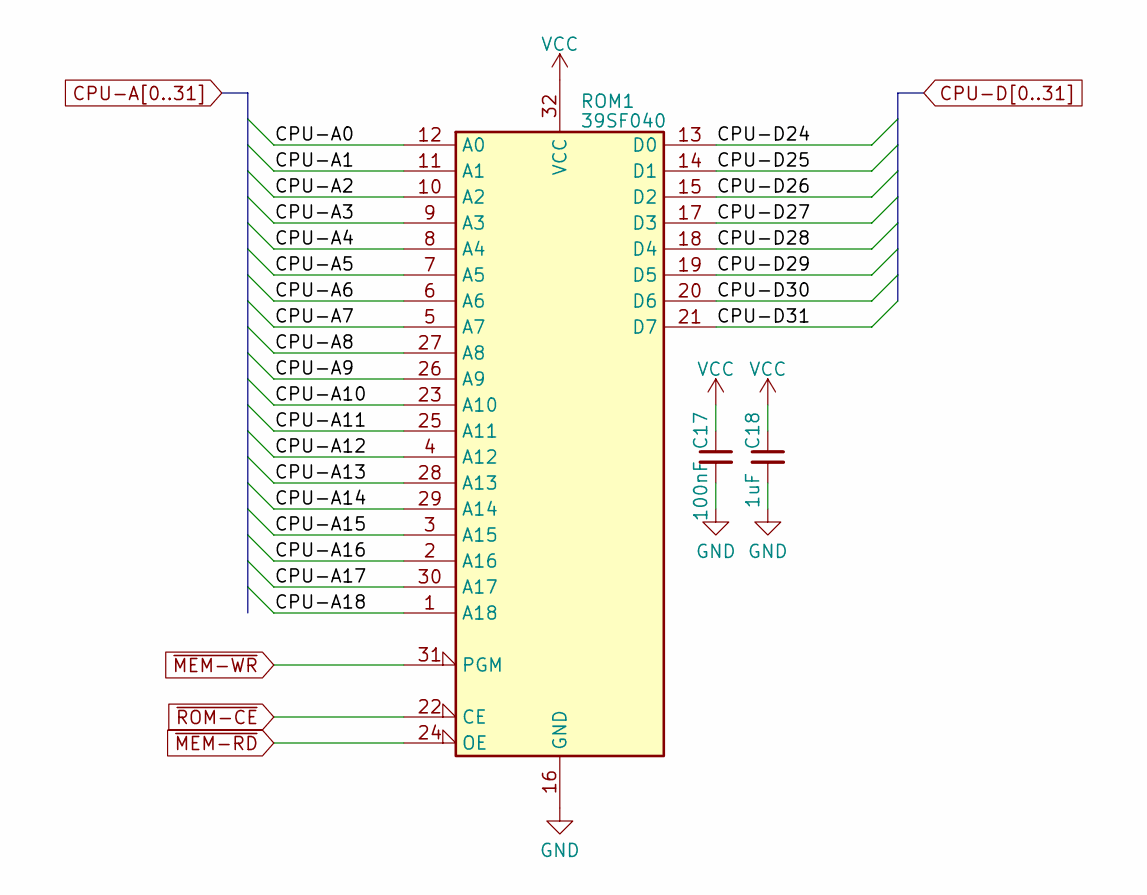
[picture p8: schematic ROM.kicad_sch]

Parts:
C17: 100nF; C_0402_1005Metric_Pad0.74x0.62mm_HandSolder; Mouser-Part 187-CL05B104KO5NNNC
C18: 1uF; C_0402_1005Metric_Pad0.74x0.62mm_HandSolder; Mouser-Part 187-CL05A105KA5NQNC
ROM1: 39SF040; PLCC-32_THT-Socket; Mouser-Part 804-39SF0407CNHE

Connections:
CPU-A0: ROM1.12 (A0)
CPU-A1: ROM1.11 (A1)
CPU-A2: ROM1.10 (A2)
CPU-A3: ROM1.9 (A3)
CPU-A4: ROM1.8 (A4)
CPU-A5: ROM1.7 (A5)
CPU-A6: ROM1.6 (A6)
CPU-A7: ROM1.5 (A7)
CPU-A8: ROM1.27 (A8)
CPU-A9: ROM1.26 (A9)
CPU-A10: ROM1.23 (A10)
CPU-A11: ROM1.25 (A11)
CPU-A12: ROM1.4 (A12)
CPU-A13: ROM1.28 (A13)
CPU-A14: ROM1.29 (A14)
CPU-A15: ROM1.3 (A15)
CPU-A16: ROM1.2 (A16)
CPU-A17: ROM1.30 (A17)
CPU-A18: ROM1.1 (A18)
CPU-D24: ROM1.13 (D0)
CPU-D25: ROM1.14 (D1)
CPU-D26: ROM1.15 (D2)
CPU-D27: ROM1.17 (D3)
CPU-D28: ROM1.18 (D4)
CPU-D29: ROM1.19 (D5)
CPU-D30: ROM1.20 (D6)
CPU-D31: ROM1.21 (D7)
GND: C17.2, C18.2, ROM1.16 (GND)
VCC: C17.1, C18.1, ROM1.32 (VCC)
~MEM-RD: ROM1.24 (OE)
~MEM-WR: ROM1.31 (PGM)
~ROM-CE: ROM1.22 (CE)
