techav-homebrew/Wrap030-ATX/Mainboard/SPIO.kicad_sch

## KiCad design Mainboard/SPIO.kicad_sch (2023-04-03)

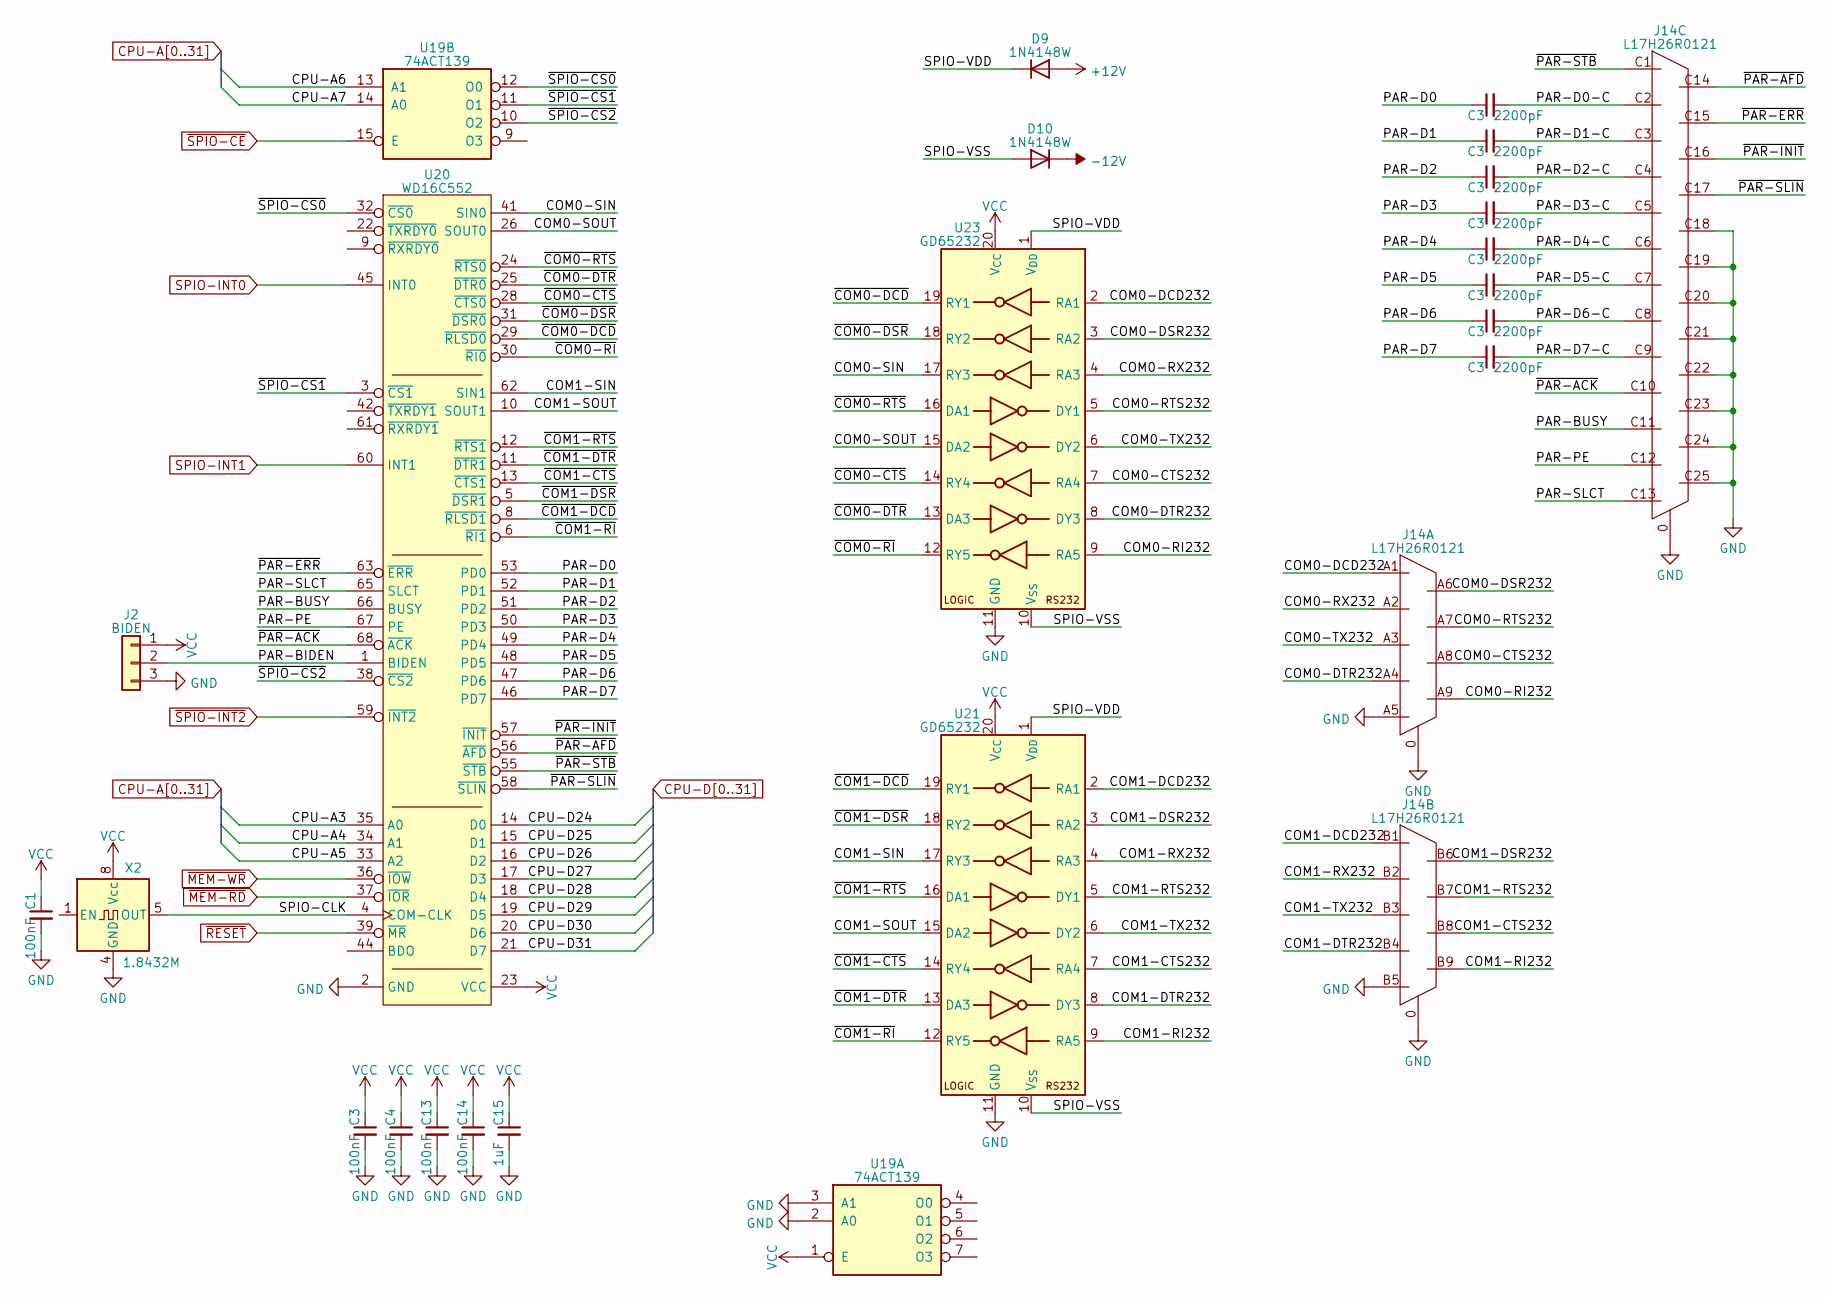
[picture p9: schematic SPIO.kicad_sch]

Parts:
C1, C4, C13, C14: 100nF; C_0402_1005Metric_Pad0.74x0.62mm_HandSolder; Mouser-Part 187-CL05B104KO5NNNC
C3: 2200pF; C_0402_1005Metric_Pad0.74x0.62mm_HandSolder; Mouser-Part 81-GRM155R71H222KA1J
C15: 1uF; C_0402_1005Metric_Pad0.74x0.62mm_HandSolder; Mouser-Part 187-CL05A105KA5NQNC
D9, D10: 1N4148W; D_SOD-123; Mouser-Part 833-1N4148W-TP
J2: BIDEN; PinHeader_1x03_P2.54mm_Vertical; Mouser-Part 523-G800W305018EU
J14: L17H26R0121; Mouser-Part 523-L17H26R0121
U19: 74ACT139; DIP-16_W7.62mm_Socket; Mouser-Part 595-CD74ACT139E
U20: WD16C552; PLCC-68_THT-Socket; Mouser-Part 595-TL16C552AIFN
U21, U23: GD65232; TSSOP-20_4.4x6.5mm_P0.65mm; Mouser-Part 595-GD65232PWR
X2: 1.8432M; Oscillator_DIP-8; Mouser-Part 520-TCH184-X

Connections:
+12V: D9.2 (A)
-12V: D10.1 (K)
COM0-CTS232: J14.A8, U23.7 (RA4)
COM0-DCD232: J14.A1, U23.2 (RA1)
COM0-DSR232: J14.A6, U23.3 (RA2)
COM0-DTR232: J14.A4, U23.8 (DY3)
COM0-RI232: J14.A9, U23.9 (RA5)
COM0-RTS232: J14.A7, U23.5 (DY1)
COM0-RX232: J14.A2, U23.4 (RA3)
COM0-SIN: U20.41 (SIN0), U23.17 (RY3)
COM0-SOUT: U20.26 (SOUT0), U23.15 (DA2)
COM0-TX232: J14.A3, U23.6 (DY2)
COM1-CTS232: J14.B8, U21.7 (RA4)
COM1-DCD232: J14.B1, U21.2 (RA1)
COM1-DSR232: J14.B6, U21.3 (RA2)
COM1-DTR232: J14.B4, U21.8 (DY3)
COM1-RI232: J14.B9, U21.9 (RA5)
COM1-RTS232: J14.B7, U21.5 (DY1)
COM1-RX232: J14.B2, U21.4 (RA3)
COM1-SIN: U20.62 (SIN1), U21.17 (RY3)
COM1-SOUT: U20.10 (SOUT1), U21.15 (DA2)
COM1-TX232: J14.B3, U21.6 (DY2)
CPU-A3: U20.35 (A0)
CPU-A4: U20.34 (A1)
CPU-A5: U20.33 (A2)
CPU-A6: U19.13 (A1)
CPU-A7: U19.14 (A0)
CPU-D24: U20.14 (D0)
CPU-D25: U20.15 (D1)
CPU-D26: U20.16 (D2)
CPU-D27: U20.17 (D3)
CPU-D28: U20.18 (D4)
CPU-D29: U20.19 (D5)
CPU-D30: U20.20 (D6)
CPU-D31: U20.21 (D7)
GND: C1.2, C3.2, C4.2, C13.2, C14.2, C15.2, J2.3, J14.0, J14.A5, J14.B5, J14.C18, J14.C19, J14.C20, J14.C21, J14.C22, J14.C23, J14.C24, J14.C25, U19.2 (A0), U19.3 (A1), U20.2 (GND), U20.7 (GND), U20.43 (GND), U20.54 (GND), U21.11 (GND), U23.11 (GND), X2.4 (GND)
PAR-BIDEN: J2.2, U20.1 (BIDEN)
PAR-BUSY: J14.C11, U20.66 (BUSY)
PAR-D0: C3.1, U20.53 (PD0)
PAR-D0-C: C3.2, J14.C2
PAR-D1: C3.1, U20.52 (PD1)
PAR-D1-C: C3.2, J14.C3
PAR-D2: C3.1, U20.51 (PD2)
PAR-D2-C: C3.2, J14.C4
PAR-D3: C3.1, U20.50 (PD3)
PAR-D3-C: C3.2, J14.C5
PAR-D4: C3.1, U20.49 (PD4)
PAR-D4-C: C3.2, J14.C6
PAR-D5: C3.1, U20.48 (PD5)
PAR-D5-C: C3.2, J14.C7
PAR-D6: C3.1, U20.47 (PD6)
PAR-D6-C: C3.2, J14.C8
PAR-D7: C3.1, U20.46 (PD7)
PAR-D7-C: C3.2, J14.C9
PAR-PE: J14.C12, U20.67 (PE)
PAR-SLCT: J14.C13, U20.65 (SLCT)
SPIO-CLK: U20.4 (COM-CLK), X2.5 (OUT)
SPIO-INT0: U20.45 (INT0)
SPIO-INT1: U20.60 (INT1)
SPIO-VDD: D9.1 (K), U21.1 (V_{DD}), U23.1 (V_{DD})
SPIO-VSS: D10.2 (A), U21.10 (V_{SS}), U23.10 (V_{SS})
VCC: C1.1, C3.1, C4.1, C13.1, C14.1, C15.1, J2.1, U19.1 (E), U20.23 (VCC), U20.27 (VCC), U20.40 (VCC), U20.64 (VCC), U21.20 (V_{CC}), U23.20 (V_{CC}), X2.8 (Vcc)
~COM0-CTS: U20.28 (~CTS0), U23.14 (RY4)
~COM0-DCD: U20.29 (~RLSD0), U23.19 (RY1)
~COM0-DSR: U20.31 (~DSR0), U23.18 (RY2)
~COM0-DTR: U20.25 (~DTR0), U23.13 (DA3)
~COM0-RI: U20.30 (~RI0), U23.12 (RY5)
~COM0-RTS: U20.24 (~RTS0), U23.16 (DA1)
~COM1-CTS: U20.13 (~CTS1), U21.14 (RY4)
~COM1-DCD: U20.8 (~RLSD1), U21.19 (RY1)
~COM1-DSR: U20.5 (~DSR1), U21.18 (RY2)
~COM1-DTR: U20.11 (~DTR1), U21.13 (DA3)
~COM1-RI: U20.6 (~RI1), U21.12 (RY5)
~COM1-RTS: U20.12 (~RTS1), U21.16 (DA1)
~MEM-RD: U20.37 (~IOR)
~MEM-WR: U20.36 (~IOW)
~PAR-ACK: J14.C10, U20.68 (~ACK)
~PAR-AFD: J14.C14, U20.56 (~AFD)
~PAR-ERR: J14.C15, U20.63 (~ERR)
~PAR-INIT: J14.C16, U20.57 (~INIT)
~PAR-SLIN: J14.C17, U20.58 (~SLIN)
~PAR-STB: J14.C1, U20.55 (~STB)
~RESET: U20.39 (~MR)
~SPIO-CE: U19.15 (E)
~SPIO-CS0: U19.12 (O0), U20.32 (~CS0)
~SPIO-CS1: U19.11 (O1), U20.3 (~CS1)
~SPIO-CS2: U19.10 (O2), U20.38 (~CS2)
~SPIO-INT2: U20.59 (~INT2)
