techav-homebrew/Wrap030-ATX/Mainboard/VidGen.kicad_sch

## KiCad design Mainboard/VidGen.kicad_sch (2023-04-03)

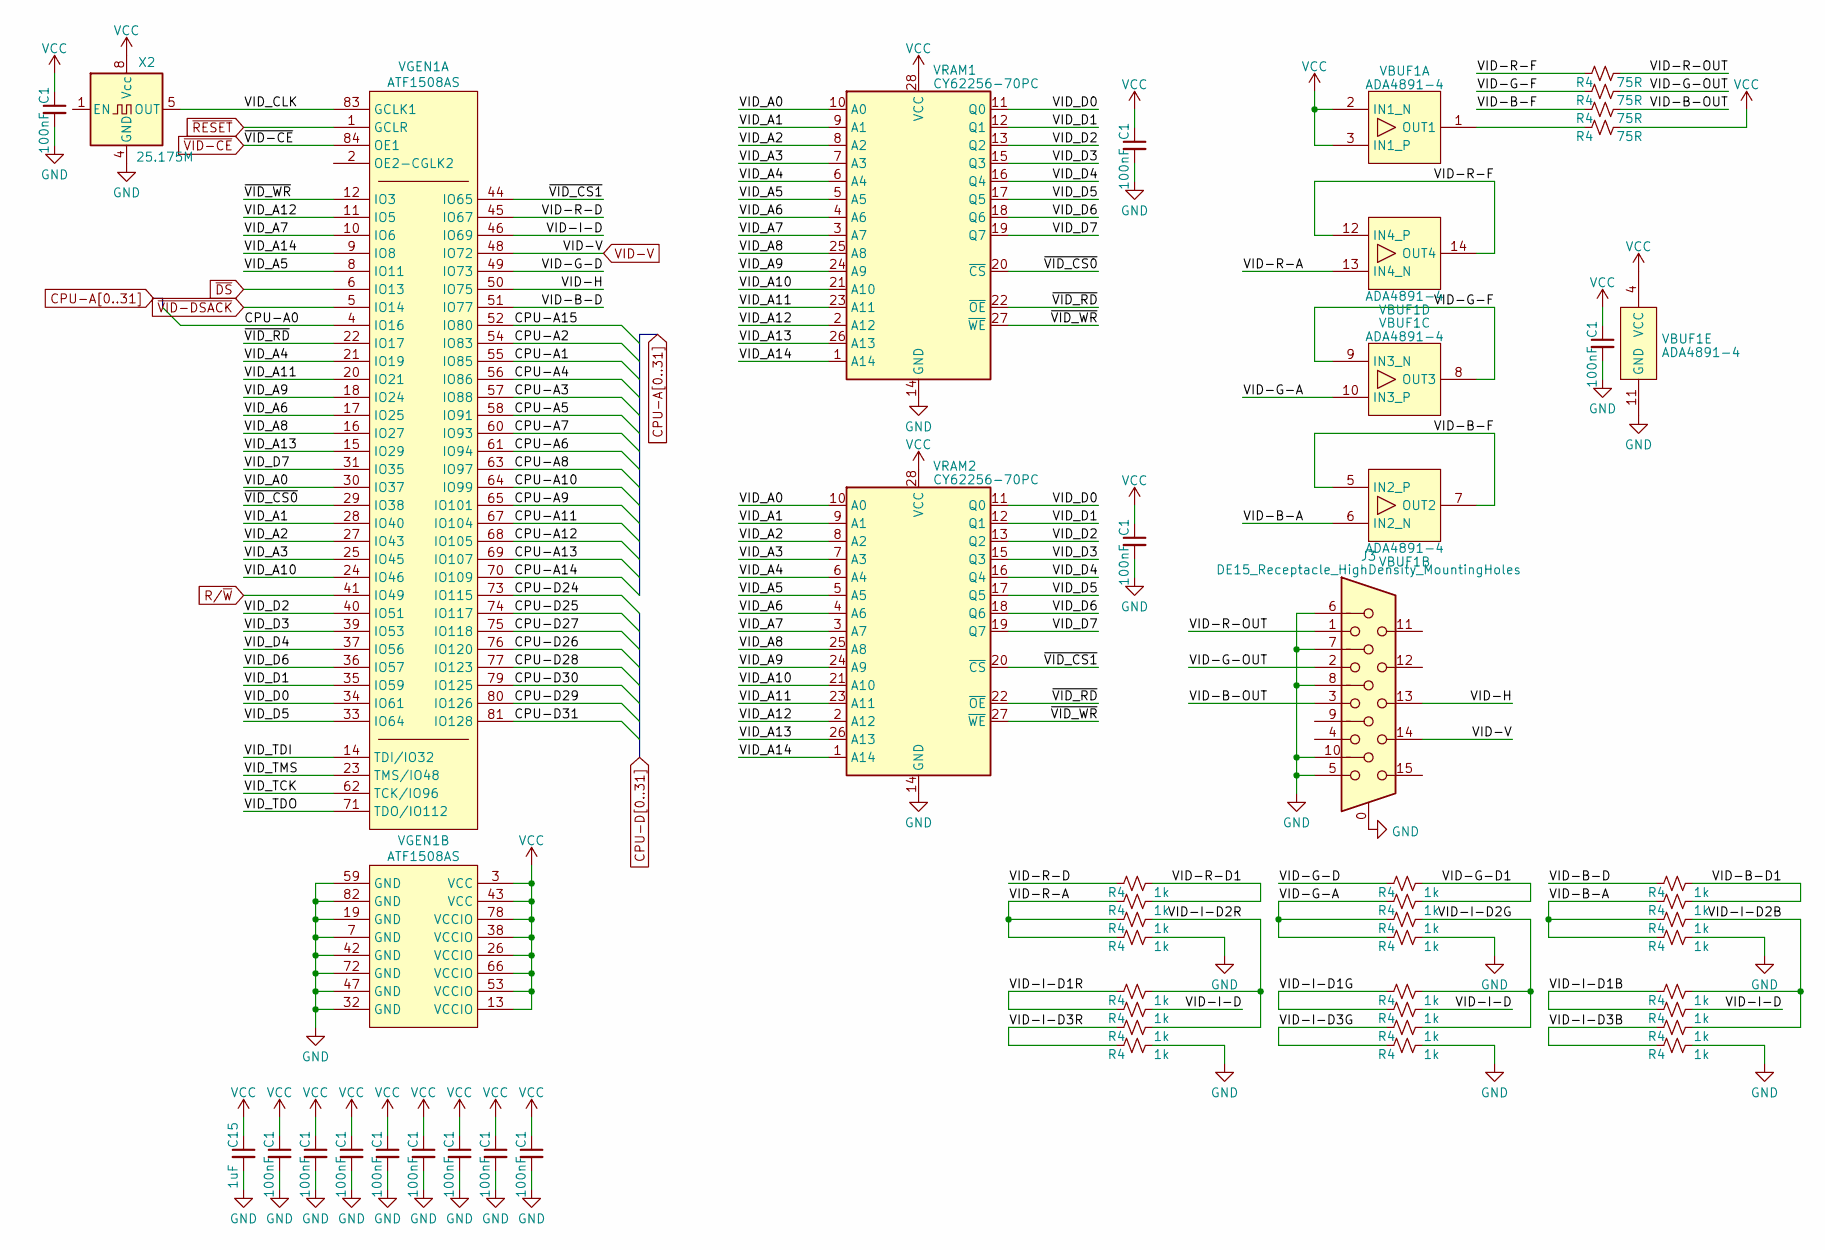
[picture p10: schematic VidGen.kicad_sch]

Parts:
C1: 100nF; C_0402_1005Metric_Pad0.74x0.62mm_HandSolder; Mouser-Part 187-CL05B104KO5NNNC
C15: 1uF; C_0402_1005Metric_Pad0.74x0.62mm_HandSolder; Mouser-Part 187-CL05A105KA5NQNC
J3: DE15_Receptacle_HighDensity_MountingHoles; DE15-HD; Mouser-Part 587-634-015-263-030
R4: 1k; R_0402_1005Metric_Pad0.72x0.64mm_HandSolder; Mouser-Part 303-0402WGF1001TCE
VBUF1: ADA4891-4; SOIC-14_3.9x8.7mm_P1.27mm; Mouser-Part 584-ADA4891-4ARZ
VGEN1: ATF1508AS; PLCC-84_THT-Socket; Mouser-Part 556-ATF1508AS-10JU84
VRAM1, VRAM2: CY62256-70PC; DIP-28_W7.62mm_Socket; Mouser-Part 972-71256SA15TPG
X2: 25.175M; Oscillator_DIP-8; Mouser-Part 774-MXO45HS-3C-25.1

Connections:
CPU-A0: VGEN1.4 (IO16)
CPU-A1: VGEN1.55 (IO85)
CPU-A2: VGEN1.54 (IO83)
CPU-A3: VGEN1.57 (IO88)
CPU-A4: VGEN1.56 (IO86)
CPU-A5: VGEN1.58 (IO91)
CPU-A6: VGEN1.61 (IO94)
CPU-A7: VGEN1.60 (IO93)
CPU-A8: VGEN1.63 (IO97)
CPU-A9: VGEN1.65 (IO101)
CPU-A10: VGEN1.64 (IO99)
CPU-A11: VGEN1.67 (IO104)
CPU-A12: VGEN1.68 (IO105)
CPU-A13: VGEN1.69 (IO107)
CPU-A14: VGEN1.70 (IO109)
CPU-A15: VGEN1.52 (IO80)
CPU-D24: VGEN1.73 (IO115)
CPU-D25: VGEN1.74 (IO117)
CPU-D26: VGEN1.76 (IO120)
CPU-D27: VGEN1.75 (IO118)
CPU-D28: VGEN1.77 (IO123)
CPU-D29: VGEN1.80 (IO126)
CPU-D30: VGEN1.79 (IO125)
CPU-D31: VGEN1.81 (IO128)
GND: C1.2, C15.2, J3.0, J3.5, J3.6, J3.7, J3.8, J3.10, R4.2, VBUF1.11 (GND), VGEN1.7 (GND), VGEN1.19 (GND), VGEN1.32 (GND), VGEN1.42 (GND), VGEN1.47 (GND), VGEN1.59 (GND), VGEN1.72 (GND), VGEN1.82 (GND), VRAM1.14 (GND), VRAM2.14 (GND), X2.4 (GND)
unnamed: R4.1, VBUF1.1 (OUT1)
R/~W: VGEN1.41 (IO49)
VCC: C1.1, C15.1, R4.2, VBUF1.2 (IN1_N), VBUF1.3 (IN1_P), VBUF1.4 (VCC), VGEN1.3 (VCC), VGEN1.13 (VCCIO), VGEN1.26 (VCCIO), VGEN1.38 (VCCIO), VGEN1.43 (VCC), VGEN1.53 (VCCIO), VGEN1.66 (VCCIO), VGEN1.78 (VCCIO), VRAM1.28 (VCC), VRAM2.28 (VCC), X2.8 (Vcc)
VID-B-A: R4.1, VBUF1.6 (IN2_N)
VID-B-D: R4.1, VGEN1.51 (IO77)
VID-B-D1: R4.2
VID-B-F: R4.1, VBUF1.5 (IN2_P), VBUF1.7 (OUT2)
VID-B-OUT: J3.3, R4.2
VID-G-A: R4.1, VBUF1.10 (IN3_P)
VID-G-D: R4.1, VGEN1.49 (IO73)
VID-G-D1: R4.2
VID-G-F: R4.1, VBUF1.8 (OUT3), VBUF1.9 (IN3_N)
VID-G-OUT: J3.2, R4.2
VID-H: J3.13, VGEN1.50 (IO75)
VID-I-D: R4.2, VGEN1.46 (IO69)
VID-I-D1B: R4.1
VID-I-D1G: R4.1
VID-I-D1R: R4.1
VID-I-D2B: R4.2
VID-I-D2G: R4.2
VID-I-D2R: R4.2
VID-I-D3B: R4.1
VID-I-D3G: R4.1
VID-I-D3R: R4.1
VID-R-A: R4.1, VBUF1.13 (IN4_N)
VID-R-D: R4.1, VGEN1.45 (IO67)
VID-R-D1: R4.2
VID-R-F: R4.1, VBUF1.12 (IN4_P), VBUF1.14 (OUT4)
VID-R-OUT: J3.1, R4.2
VID-V: J3.14, VGEN1.48 (IO72)
VID_A0: VGEN1.30 (IO37), VRAM1.10 (A0), VRAM2.10 (A0)
VID_A1: VGEN1.28 (IO40), VRAM1.9 (A1), VRAM2.9 (A1)
VID_A2: VGEN1.27 (IO43), VRAM1.8 (A2), VRAM2.8 (A2)
VID_A3: VGEN1.25 (IO45), VRAM1.7 (A3), VRAM2.7 (A3)
VID_A4: VGEN1.21 (IO19), VRAM1.6 (A4), VRAM2.6 (A4)
VID_A5: VGEN1.8 (IO11), VRAM1.5 (A5), VRAM2.5 (A5)
VID_A6: VGEN1.17 (IO25), VRAM1.4 (A6), VRAM2.4 (A6)
VID_A7: VGEN1.10 (IO6), VRAM1.3 (A7), VRAM2.3 (A7)
VID_A8: VGEN1.16 (IO27), VRAM1.25 (A8), VRAM2.25 (A8)
VID_A9: VGEN1.18 (IO24), VRAM1.24 (A9), VRAM2.24 (A9)
VID_A10: VGEN1.24 (IO46), VRAM1.21 (A10), VRAM2.21 (A10)
VID_A11: VGEN1.20 (IO21), VRAM1.23 (A11), VRAM2.23 (A11)
VID_A12: VGEN1.11 (IO5), VRAM1.2 (A12), VRAM2.2 (A12)
VID_A13: VGEN1.15 (IO29), VRAM1.26 (A13), VRAM2.26 (A13)
VID_A14: VGEN1.9 (IO8), VRAM1.1 (A14), VRAM2.1 (A14)
VID_CLK: VGEN1.83 (GCLK1), X2.5 (OUT)
VID_D0: VGEN1.34 (IO61), VRAM1.11 (Q0), VRAM2.11 (Q0)
VID_D1: VGEN1.35 (IO59), VRAM1.12 (Q1), VRAM2.12 (Q1)
VID_D2: VGEN1.40 (IO51), VRAM1.13 (Q2), VRAM2.13 (Q2)
VID_D3: VGEN1.39 (IO53), VRAM1.15 (Q3), VRAM2.15 (Q3)
VID_D4: VGEN1.37 (IO56), VRAM1.16 (Q4), VRAM2.16 (Q4)
VID_D5: VGEN1.33 (IO64), VRAM1.17 (Q5), VRAM2.17 (Q5)
VID_D6: VGEN1.36 (IO57), VRAM1.18 (Q6), VRAM2.18 (Q6)
VID_D7: VGEN1.31 (IO35), VRAM1.19 (Q7), VRAM2.19 (Q7)
VID_TCK: VGEN1.62 (TCK/IO96)
VID_TDI: VGEN1.14 (TDI/IO32)
VID_TDO: VGEN1.71 (TDO/IO112)
VID_TMS: VGEN1.23 (TMS/IO48)
~DS: VGEN1.6 (IO13)
~RESET: VGEN1.1 (GCLR)
~VID-CE: VGEN1.84 (OE1)
~VID-DSACK: VGEN1.5 (IO14)
~VID_CS0: VGEN1.29 (IO38), VRAM1.20 (~CS)
~VID_CS1: VGEN1.44 (IO65), VRAM2.20 (~CS)
~VID_RD: VGEN1.22 (IO17), VRAM1.22 (~OE), VRAM2.22 (~OE)
~VID_WR: VGEN1.12 (IO3), VRAM1.27 (~WE), VRAM2.27 (~WE)
