techav-homebrew/Wrap030-ATX/Mainboard/cpu-fpu.kicad_sch

## KiCad design Mainboard/cpu-fpu.kicad_sch (2023-04-03)

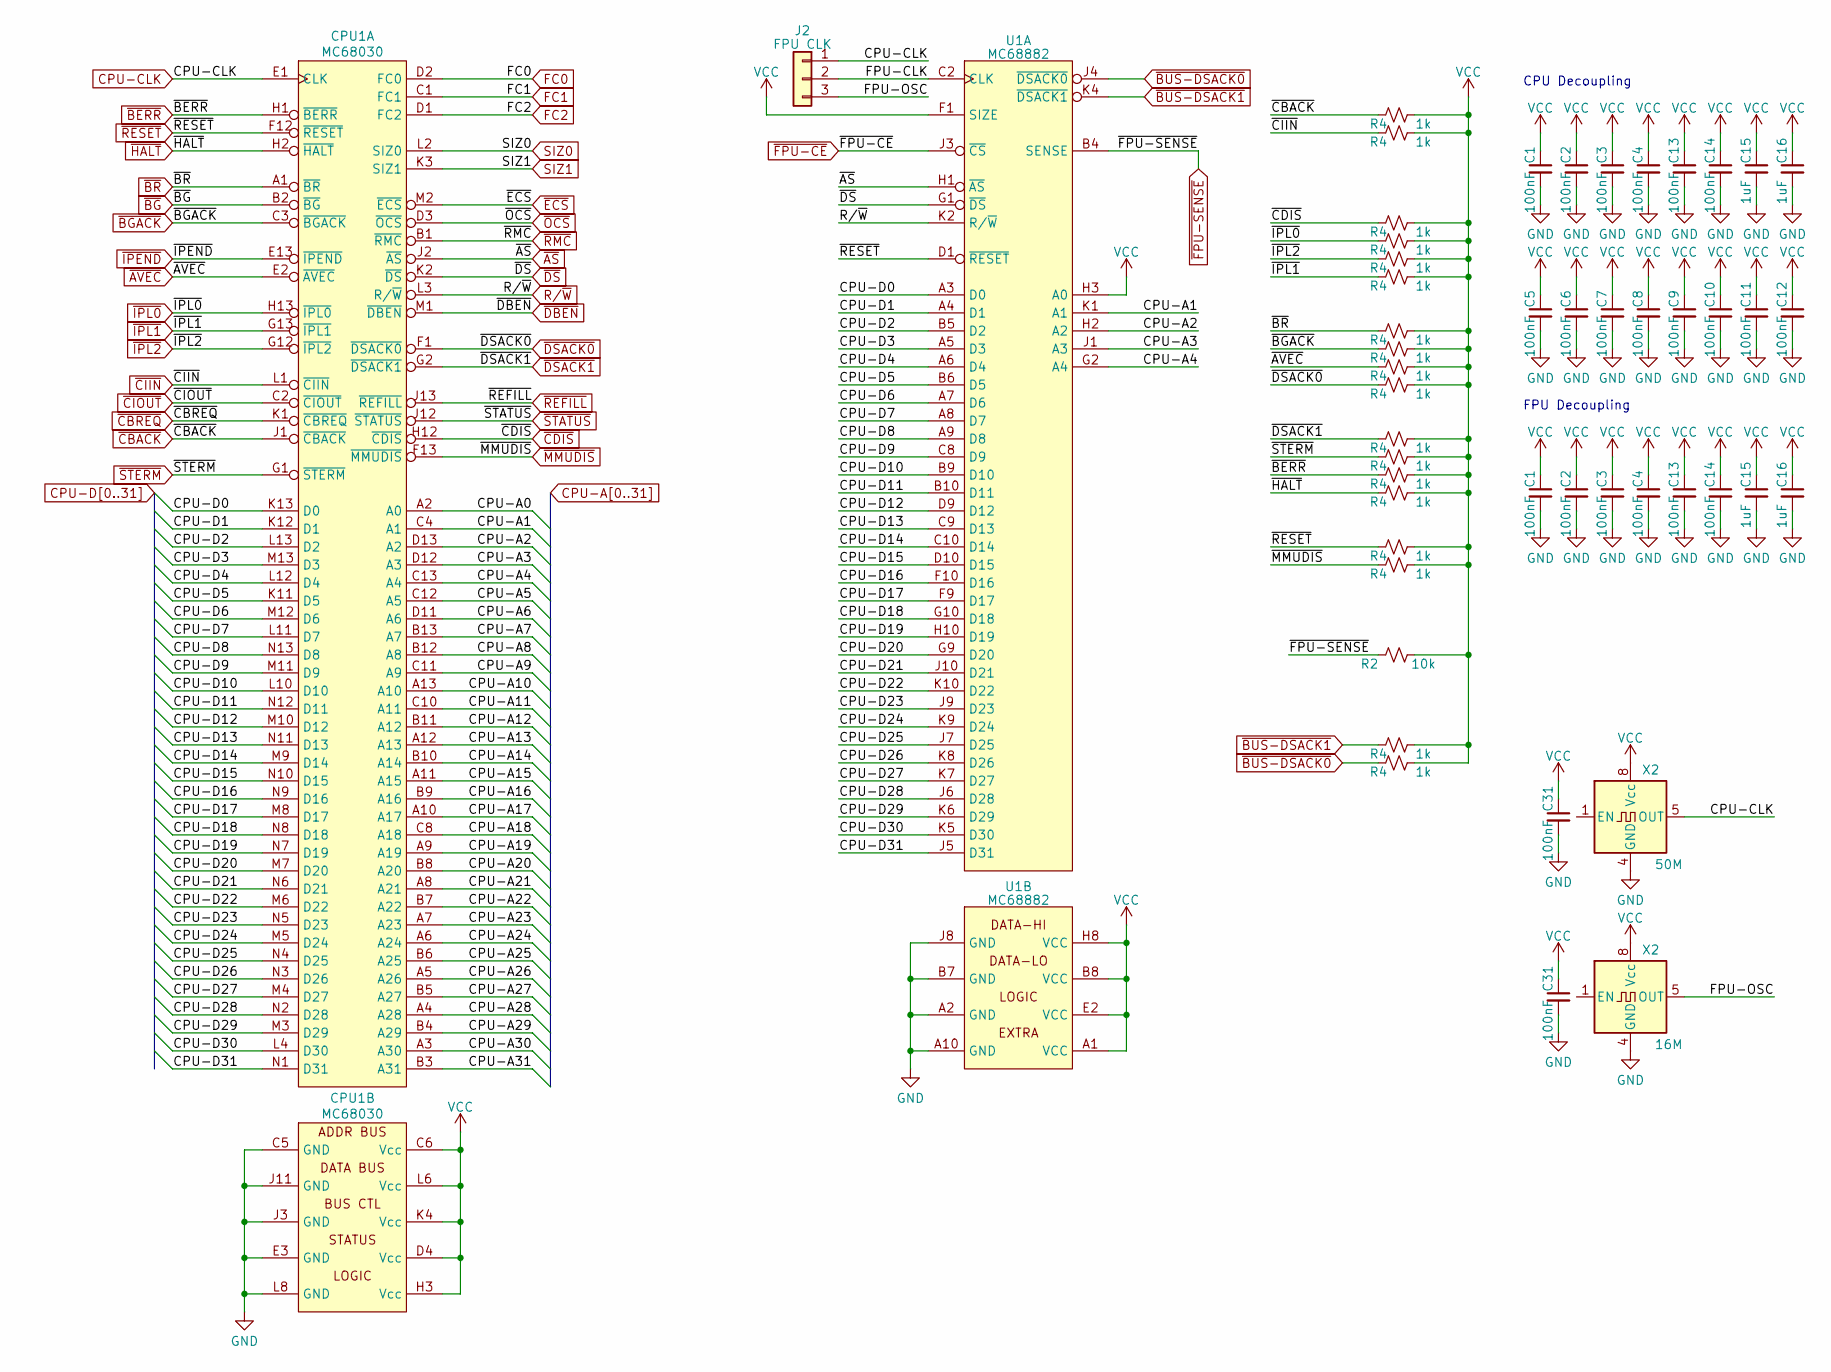
[picture p11: schematic cpu-fpu.kicad_sch]

Parts:
C1, C2, C3, C4, C5, C6, C7, C8, C9, C10, C11, C12, C13, C14, C31: 100nF; C_0402_1005Metric_Pad0.74x0.62mm_HandSolder; Mouser-Part 187-CL05B104KO5NNNC
C15, C16: 1uF; C_0402_1005Metric_Pad0.74x0.62mm_HandSolder; Mouser-Part 187-CL05A105KA5NQNC
CPU1: MC68030; PGA128
J2: FPU CLK; PinHeader_1x03_P2.54mm_Vertical; Mouser-Part 523-G800W305018EU
R2: 10k; R_0402_1005Metric_Pad0.72x0.64mm_HandSolder; Mouser-Part 303-0402WGF1002TCE
R4: 1k; R_0402_1005Metric_Pad0.72x0.64mm_HandSolder; Mouser-Part 303-0402WGF1001TCE
U1: MC68882; PGA68
X2: 50M; Oscillator_DIP-8; Mouser-Part 815-ACH-50-EK

Connections:
CPU-A0: CPU1.A2 (A0)
CPU-A1: CPU1.C4 (A1), U1.K1 (A1)
CPU-A2: CPU1.D13 (A2), U1.H2 (A2)
CPU-A3: CPU1.D12 (A3), U1.J1 (A3)
CPU-A4: CPU1.C13 (A4), U1.G2 (A4)
CPU-A5: CPU1.C12 (A5)
CPU-A6: CPU1.D11 (A6)
CPU-A7: CPU1.B13 (A7)
CPU-A8: CPU1.B12 (A8)
CPU-A9: CPU1.C11 (A9)
CPU-A10: CPU1.A13 (A10)
CPU-A11: CPU1.C10 (A11)
CPU-A12: CPU1.B11 (A12)
CPU-A13: CPU1.A12 (A13)
CPU-A14: CPU1.B10 (A14)
CPU-A15: CPU1.A11 (A15)
CPU-A16: CPU1.B9 (A16)
CPU-A17: CPU1.A10 (A17)
CPU-A18: CPU1.C8 (A18)
CPU-A19: CPU1.A9 (A19)
CPU-A20: CPU1.B8 (A20)
CPU-A21: CPU1.A8 (A21)
CPU-A22: CPU1.B7 (A22)
CPU-A23: CPU1.A7 (A23)
CPU-A24: CPU1.A6 (A24)
CPU-A25: CPU1.B6 (A25)
CPU-A26: CPU1.A5 (A26)
CPU-A27: CPU1.B5 (A27)
CPU-A28: CPU1.A4 (A28)
CPU-A29: CPU1.B4 (A29)
CPU-A30: CPU1.A3 (A30)
CPU-A31: CPU1.B3 (A31)
CPU-CLK: CPU1.E1 (CLK), J2.1, X2.5 (OUT)
CPU-D0: CPU1.K13 (D0), U1.A3 (D0)
CPU-D1: CPU1.K12 (D1), U1.A4 (D1)
CPU-D2: CPU1.L13 (D2), U1.B5 (D2)
CPU-D3: CPU1.M13 (D3), U1.A5 (D3)
CPU-D4: CPU1.L12 (D4), U1.A6 (D4)
CPU-D5: CPU1.K11 (D5), U1.B6 (D5)
CPU-D6: CPU1.M12 (D6), U1.A7 (D6)
CPU-D7: CPU1.L11 (D7), U1.A8 (D7)
CPU-D8: CPU1.N13 (D8), U1.A9 (D8)
CPU-D9: CPU1.M11 (D9), U1.C8 (D9)
CPU-D10: CPU1.L10 (D10), U1.B9 (D10)
CPU-D11: CPU1.N12 (D11), U1.B10 (D11)
CPU-D12: CPU1.M10 (D12), U1.D9 (D12)
CPU-D13: CPU1.N11 (D13), U1.C9 (D13)
CPU-D14: CPU1.M9 (D14), U1.C10 (D14)
CPU-D15: CPU1.N10 (D15), U1.D10 (D15)
CPU-D16: CPU1.N9 (D16), U1.F10 (D16)
CPU-D17: CPU1.M8 (D17), U1.F9 (D17)
CPU-D18: CPU1.N8 (D18), U1.G10 (D18)
CPU-D19: CPU1.N7 (D19), U1.H10 (D19)
CPU-D20: CPU1.M7 (D20), U1.G9 (D20)
CPU-D21: CPU1.N6 (D21), U1.J10 (D21)
CPU-D22: CPU1.M6 (D22), U1.K10 (D22)
CPU-D23: CPU1.N5 (D23), U1.J9 (D23)
CPU-D24: CPU1.M5 (D24), U1.K9 (D24)
CPU-D25: CPU1.N4 (D25), U1.J7 (D25)
CPU-D26: CPU1.N3 (D26), U1.K8 (D26)
CPU-D27: CPU1.M4 (D27), U1.K7 (D27)
CPU-D28: CPU1.N2 (D28), U1.J6 (D28)
CPU-D29: CPU1.M3 (D29), U1.K6 (D29)
CPU-D30: CPU1.L4 (D30), U1.K5 (D30)
CPU-D31: CPU1.N1 (D31), U1.J5 (D31)
FC0: CPU1.D2 (FC0)
FC1: CPU1.C1 (FC1)
FC2: CPU1.D1 (FC2)
FPU-CLK: J2.2, U1.C2 (CLK)
FPU-OSC: J2.3, X2.5 (OUT)
GND: C1.2, C2.2, C3.2, C4.2, C5.2, C6.2, C7.2, C8.2, C9.2, C10.2, C11.2, C12.2, C13.2, C14.2, C15.2, C16.2, C31.2, CPU1.C5 (GND), CPU1.C7 (GND), CPU1.C9 (GND), CPU1.E3 (GND), CPU1.E11 (GND), CPU1.F3 (GND), CPU1.G3 (GND), CPU1.G11 (GND), CPU1.J3 (GND), CPU1.J11 (GND), CPU1.L5 (GND), CPU1.L7 (GND), CPU1.L8 (GND), CPU1.L9 (GND), U1.A2 (GND), U1.A10 (GND), U1.B2 (GND), U1.B3 (GND), U1.B7 (GND), U1.C1 (GND), U1.C3 (GND), U1.D2 (GND), U1.E10 (GND), U1.F2 (GND), U1.H9 (GND), U1.J8 (GND), U1.K3 (GND), X2.4 (GND)
unnamed: CPU1.D5 (NC), CPU1.E12 (NC), CPU1.F4 (NC), CPU1.F10 (NC), CPU1.K5 (NC)
R/~W: CPU1.L3 (R/~W), U1.K2 (R/~W)
SIZ0: CPU1.L2 (SIZ0)
SIZ1: CPU1.K3 (SIZ1)
VCC: C1.1, C2.1, C3.1, C4.1, C5.1, C6.1, C7.1, C8.1, C9.1, C10.1, C11.1, C12.1, C13.1, C14.1, C15.1, C16.1, C31.1, CPU1.C6 (Vcc), CPU1.D4 (Vcc), CPU1.D10 (Vcc), CPU1.F2 (Vcc), CPU1.F11 (Vcc), CPU1.H3 (Vcc), CPU1.H11 (Vcc), CPU1.K4 (Vcc), CPU1.K10 (Vcc), CPU1.L6 (Vcc), R2.2, R4.2, U1.A1 (VCC), U1.B1 (VCC), U1.B8 (VCC), U1.E2 (VCC), U1.E9 (VCC), U1.F1 (SIZE), U1.H3 (A0), U1.H8 (VCC), U1.J2 (VCC), X2.8 (Vcc)
~AS: CPU1.J2 (~AS), U1.H1 (~AS)
~AVEC: CPU1.E2 (~AVEC), R4.1
~BERR: CPU1.H1 (~BERR), R4.1
~BGACK: CPU1.C3 (~BGACK), R4.1
~BG: CPU1.B2 (~BG)
~BR: CPU1.A1 (~BR), R4.1
~BUS-DSACK0: R4.1, U1.J4 (~DSACK0)
~BUS-DSACK1: R4.1, U1.K4 (~DSACK1)
~CBACK: CPU1.J1 (~CBACK), R4.1
~CBREQ: CPU1.K1 (~CBREQ)
~CDIS: CPU1.H12 (~CDIS), R4.1
~CIIN: CPU1.L1 (~CIIN), R4.1
~CIOUT: CPU1.C2 (~CIOUT)
~DBEN: CPU1.M1 (~DBEN)
~DSACK0: CPU1.F1 (~DSACK0), R4.1
~DSACK1: CPU1.G2 (~DSACK1), R4.1
~DS: CPU1.K2 (~DS), U1.G1 (~DS)
~ECS: CPU1.M2 (~ECS)
~FPU-CE: U1.J3 (~CS)
~FPU-SENSE: R2.1, U1.B4 (SENSE)
~HALT: CPU1.H2 (~HALT), R4.1
~IPEND: CPU1.E13 (~IPEND)
~IPL0: CPU1.H13 (~IPL0), R4.1
~IPL1: CPU1.G13 (~IPL1), R4.1
~IPL2: CPU1.G12 (~IPL2), R4.1
~MMUDIS: CPU1.F13 (~MMUDIS), R4.1
~OCS: CPU1.D3 (~OCS)
~REFILL: CPU1.J13 (~REFILL)
~RESET: CPU1.F12 (~RESET), R4.1, U1.D1 (~RESET)
~RMC: CPU1.B1 (~RMC)
~STATUS: CPU1.J12 (~STATUS)
~STERM: CPU1.G1 (~STERM), R4.1

Notes on the sheet:
FPU Decoupling
CPU Decoupling
