techav-homebrew/Wrap030-ATX/Mainboard/keyboard.kicad_sch

## KiCad design Mainboard/keyboard.kicad_sch (2023-04-03)

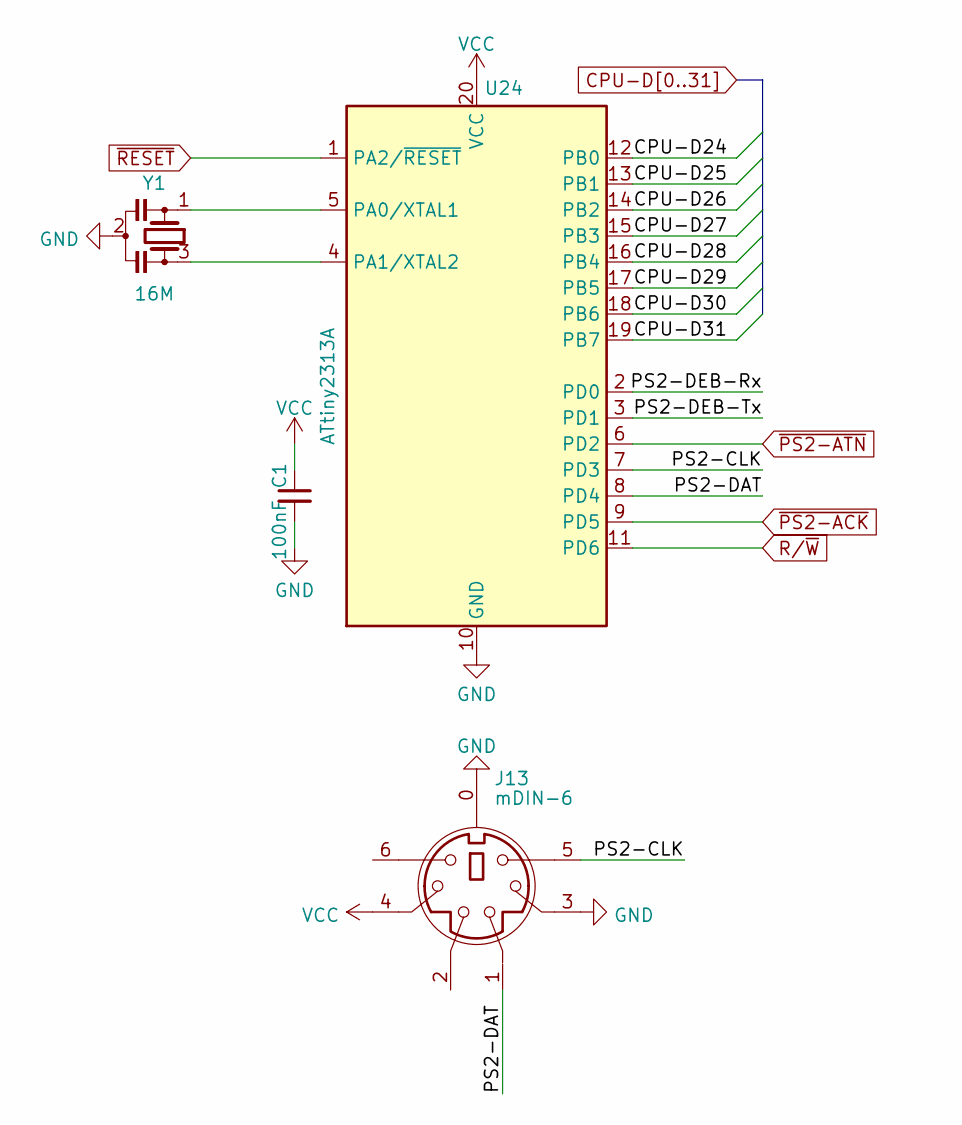
[picture p12: schematic keyboard.kicad_sch]

Parts:
C1: 100nF; C_0402_1005Metric_Pad0.74x0.62mm_HandSolder; Mouser-Part 187-CL05B104KO5NNNC
J13: mDIN-6; MiniDIN6; Mouser-Part 571-5749266-1
U24: ATtiny2313A; DIP-20_W7.62mm; Mouser-Part 556-ATTINY2313A-PU
Y1: 16M; Resonator-3Pin_W7.0mm_H2.5mm; Mouser-Part 81-CSTLS16M0X55-B0

Connections:
CPU-D24: U24.12 (PB0)
CPU-D25: U24.13 (PB1)
CPU-D26: U24.14 (PB2)
CPU-D27: U24.15 (PB3)
CPU-D28: U24.16 (PB4)
CPU-D29: U24.17 (PB5)
CPU-D30: U24.18 (PB6)
CPU-D31: U24.19 (PB7)
GND: C1.2, J13.0, J13.3, U24.10 (GND), Y1.2
unnamed: U24.4 (PA1/XTAL2), Y1.3
unnamed: U24.5 (PA0/XTAL1), Y1.1
PS2-CLK: J13.5, U24.7 (PD3)
PS2-DAT: J13.1, U24.8 (PD4)
PS2-DEB-Rx: U24.2 (PD0)
PS2-DEB-Tx: U24.3 (PD1)
R/~W: U24.11 (PD6)
VCC: C1.1, J13.4, U24.20 (VCC)
~PS2-ACK: U24.9 (PD5)
~PS2-ATN: U24.6 (PD2)
~RESET: U24.1 (PA2/~RESET)
