techav-homebrew/Wrap030-ATX/Mainboard/power.kicad_sch

## KiCad design Mainboard/power.kicad_sch (2023-04-03)

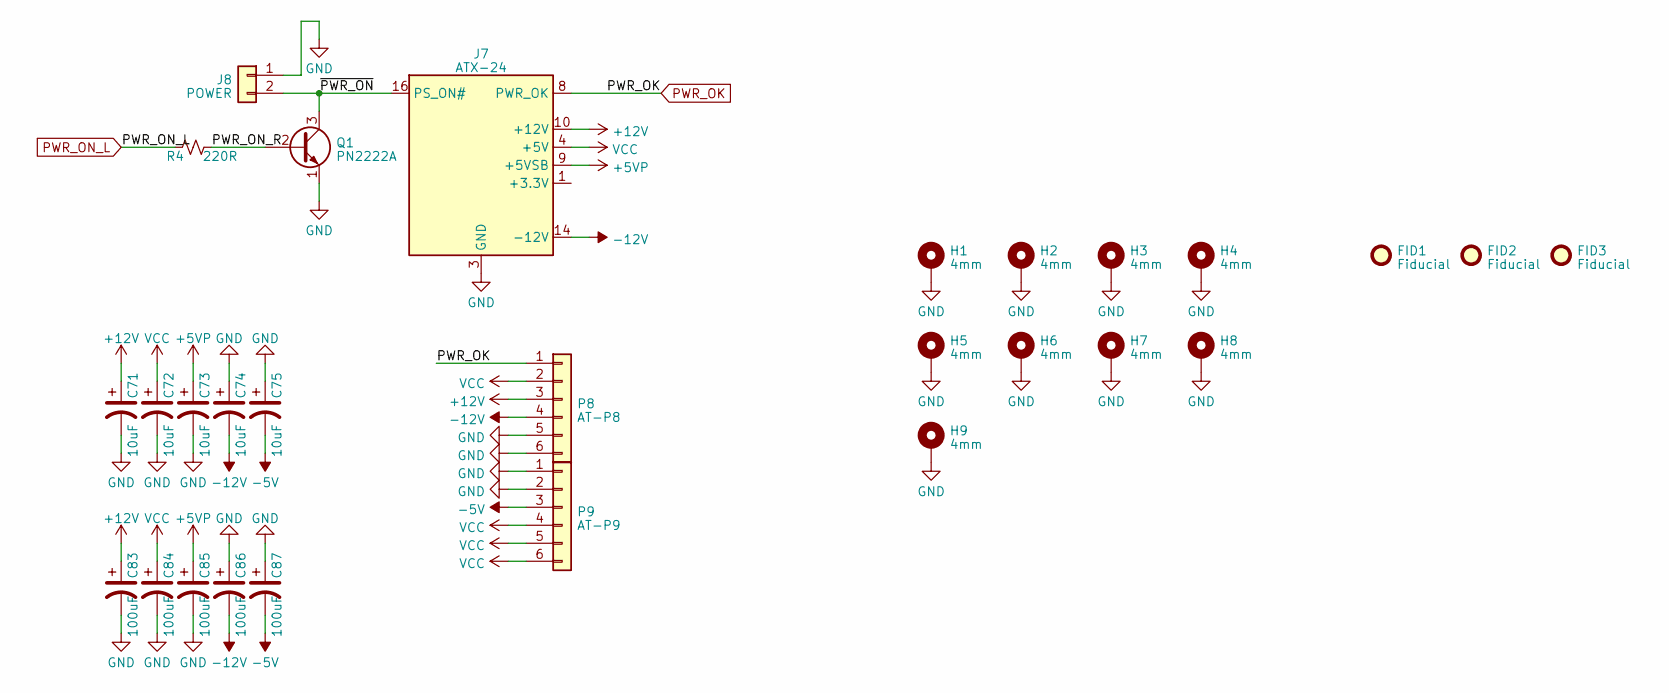
[picture p13: schematic power.kicad_sch]

Parts:
C71, C72, C73, C74, C75: 10uF; CP_Radial_D5.0mm_P2.50mm; Mouser-Part 710-860010372001
C83, C84, C85, C86, C87: 100uF; CP_Radial_D7.5mm_P2.50mm; Mouser-Part 710-860010473007
FID1, FID2, FID3: Fiducial; Fiducial_1mm_Mask2mm
H1, H2, H3, H4, H5, H6, H7, H8, H9: 4mm; MountingHole_4mm_Pad_Via
J7: ATX-24; Molex_Mini-Fit_Jr_5566-24A_2x12_P4.20mm_Vertical; Mouser-Part 538-39-28-8240
J8: POWER; PinHeader_1x02_P2.54mm_Vertical; Mouser-Part 523-G800NA306018EU
P8: AT-P8; Molex_KK-396_A-41791-0006_1x06_P3.96mm_Vertical; Mouser-Part 538-26-60-4060
P9: AT-P9; Molex_KK-396_A-41791-0006_1x06_P3.96mm_Vertical; Mouser-Part 538-26-60-4060
Q1: PN2222A; TO-92L_Inline; Mouser-Part 512-PN2222ABU
R4: 220R; R_0402_1005Metric_Pad0.72x0.64mm_HandSolder; Mouser-Part 303-0402WGF2200TCE

Connections:
+5VP: C73.1, C85.1, J7.9 (+5VSB)
+12V: C71.1, C83.1, J7.10 (+12V), J7.11 (+12V), P8.3
-5V: C75.2, C87.2, P9.3
-12V: C74.2, C86.2, J7.14 (-12V), P8.4
GND: C71.2, C72.2, C73.2, C74.1, C75.1, C83.2, C84.2, C85.2, C86.1, C87.1, H1.1, H2.1, H3.1, H4.1, H5.1, H6.1, H7.1, H8.1, H9.1, J7.3 (GND), J7.5 (GND), J7.7 (GND), J7.15 (GND), J7.17 (GND), J7.18 (GND), J7.19 (GND), J7.24 (GND), J8.1, P8.5, P8.6, P9.1, P9.2, Q1.1 (E)
unnamed: J7.1 (+3.3V), J7.2 (+3.3V), J7.12 (+3.3V), J7.13 (+3.3V)
PWR_OK: J7.8 (PWR_OK), P8.1
PWR_ON_L: R4.1
PWR_ON_R: Q1.2 (B), R4.2
VCC: C72.1, C84.1, J7.4 (+5V), J7.6 (+5V), J7.21 (+5V), J7.22 (+5V), J7.23 (+5V), P8.2, P9.4, P9.5, P9.6
~PWR_ON: J7.16 (PS_ON#), J8.2, Q1.3 (C)
