techav-homebrew/Wrap030-ATX/ExpansionBoards/Mezzanine/Glue-Logic/Mezzanine-Glue.sv

/******************************************************************************
 * Wrap030 Mezzanine Glue Logic
 * techav
 * 2022-10-28
 ******************************************************************************
 * Glue logic 
 *****************************************************************************/

module mezGlue (
    input   wire                nReset,     // primary system reset         1
    input   wire                nAS,        // address strobe               35
    input   wire                nDS,        // cpu data strobe              41
    input   wire                sysClk,     // primary system clock         2
    input   wire                fpuClk,     // fpu clock                    43
    input   wire                RnW,        // cpu read/write signal        34
    input   wire                addr31,     // address bit 31               15
    input   wire [1:0]          cpuFC,      // cpu function code            14,11
    input   wire [1:0]          siz,        // transfer size bits           17,19
    input   wire [6:0]          addrSel,    // address select bits (19:13)  28-24,21-20
    inout   wire                znBerr,     // cpu bus error                18
    inout   wire [1:0]          znDsack,    // cpu data strobe acknowledge  29,31
    output  wire                nIORd,      // ide io read strobe           5
    output  wire                nIOWr,      // ide io write strobe          40
    output  wire                nIdeBufEn,  // ide buffer enable            12
    input   wire                nIdeIO16,   // ide 16-bit signal            9
    output  wire                nIdeCS3,    // ide CE3 signal               8
    output  wire                nIdeCS1,    // ide CE1 signal               6
    output  wire                nIdeCE,     // ide enable signal            4
    output  wire                nFpuCE,     // fpu enabale signal           33
    input   wire                nFpuSense,  // fpu presence detect signal   37
);

/*****************************************************************************/
// FPU logic
always_comb begin
    // this is asynchronous because of timing requirements which require the
    // FPU-CE signal to be asserted before the falling edge of !AS, which we
    // can't really do while synchronized to the CPU clock or the slower
    // FPU clock
    if(cpuFS == 2'b11 && addrSel == 7'b0010001) nFpuCE <= 0;
    else nFpuCE <= 1;
end

// bus error if the FPU is not detected
reg fpuBerr;
always @(posedge sysClk or negedge nReset) begin
    if(!nReset) begin
        fpuBerr <= 1'b0;
    end else if(cpuFS == 2'b11 && addrSel == 7'b0010001 && !nAS && nFpuSense) begin
        fpuBerr <= 1'b1;
    end else begin
        fpuBerr <= 1'b0;
    end
end
always_comb begin
    if(fpuBerr) znBerr <= 1'b0;
    else znBerr <= 1'bZ;
end
// and that's all we need for the FPU?

/*****************************************************************************/
// IDE logic

/*****************************************************************************/
endmodule
